yellobyte/ESP32-Webradio-PlusDLNA/Doc/ESP32-Radio Front.jpg

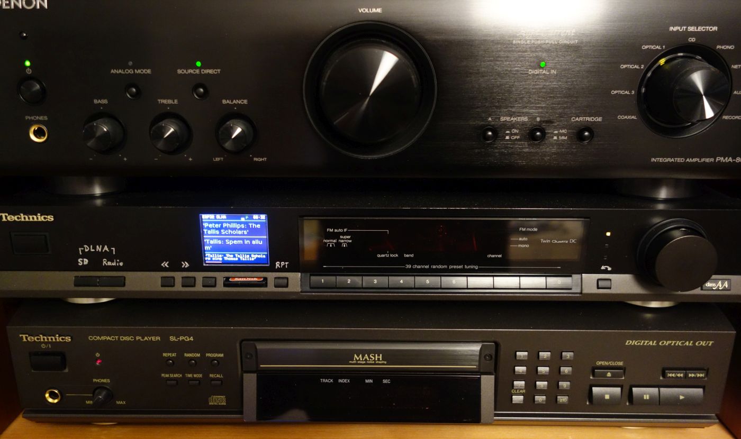
Doc/ESP32-Radio Front.jpg
