yellobyte/ESP32-Webradio-PlusDLNA/Doc/I2S to OPT Board Bottom.JPG

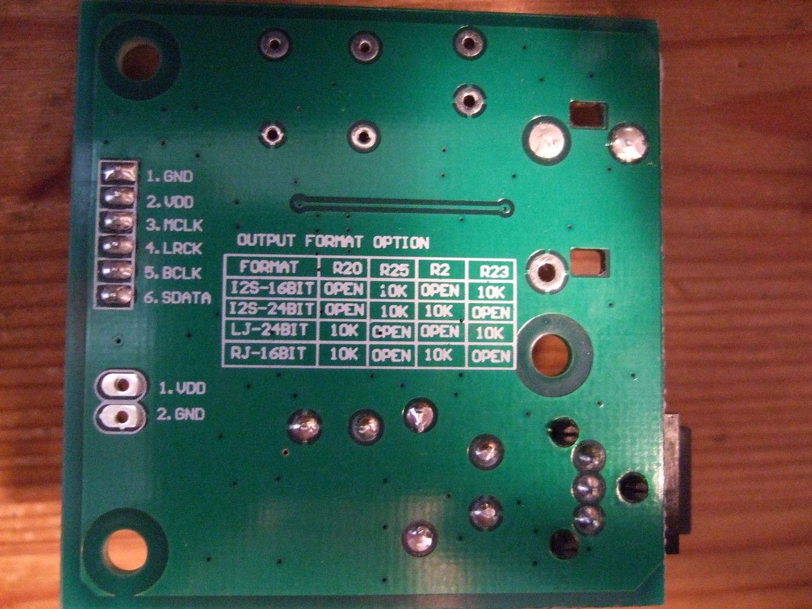
Doc/I2S to OPT Board Bottom.JPG
