yellobyte/ESP32-Webradio-PlusDLNA/Doc/I2S to OPT Board Top.JPG

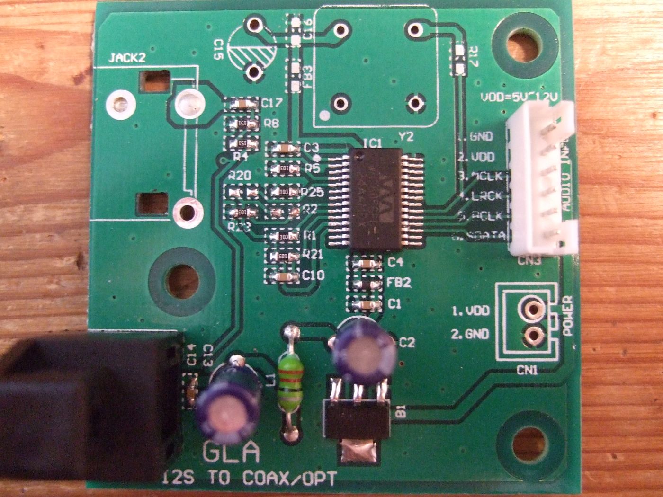
Doc/I2S to OPT Board Top.JPG
