yellobyte/ESP32-Webradio-PlusDLNA/Doc/Main Board.jpg

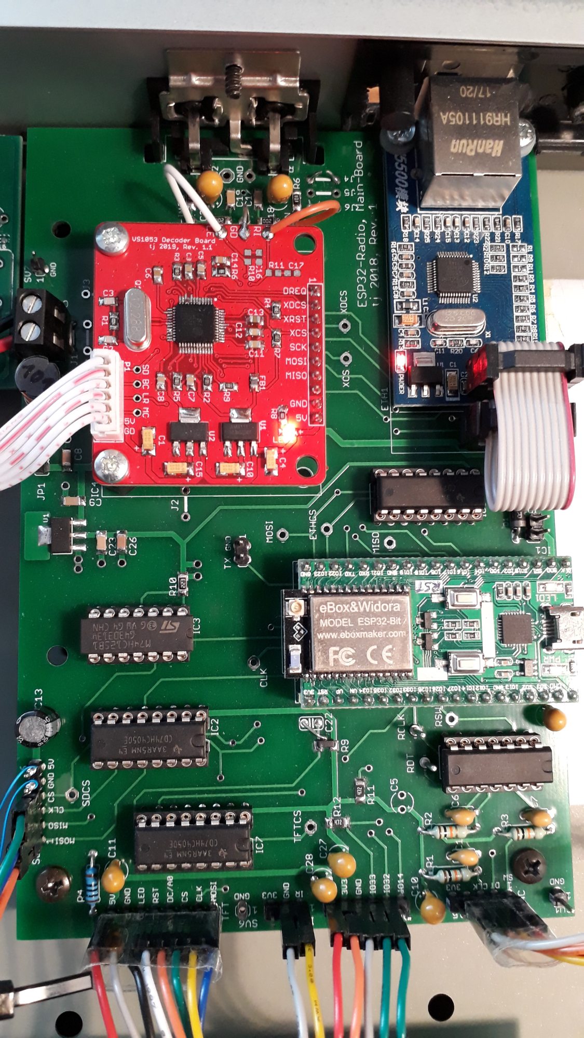
Doc/Main Board.jpg
