yellobyte/ESP32-Webradio-PlusDLNA/Doc/Open Case.jpg

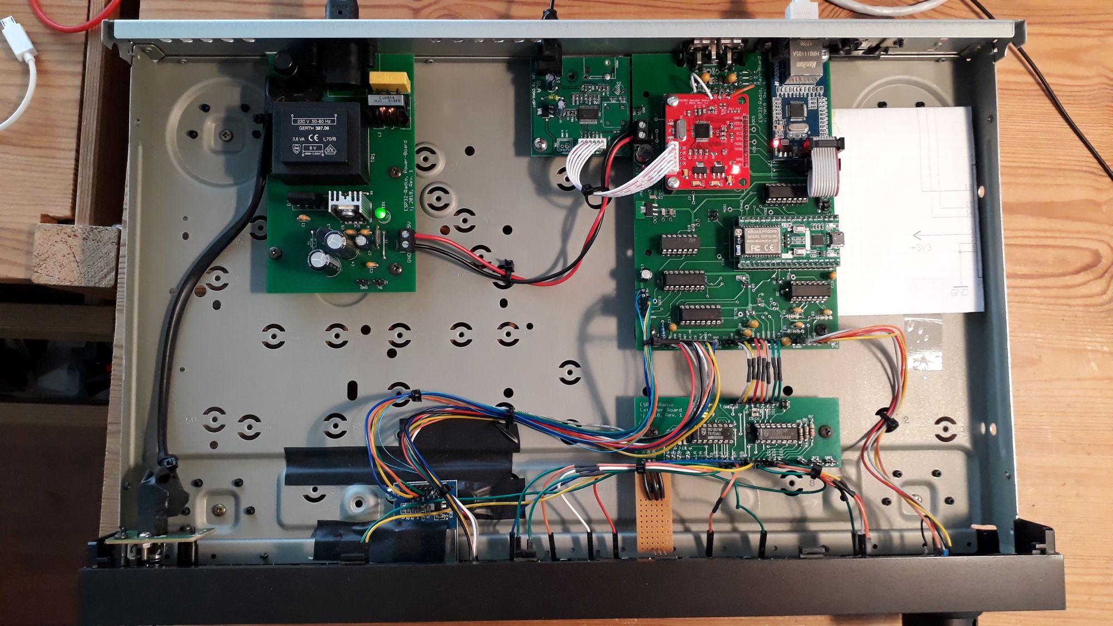
Doc/Open Case.jpg
