yellobyte/ESP32-Webradio-PlusDLNA/Doc/Power Board.jpg

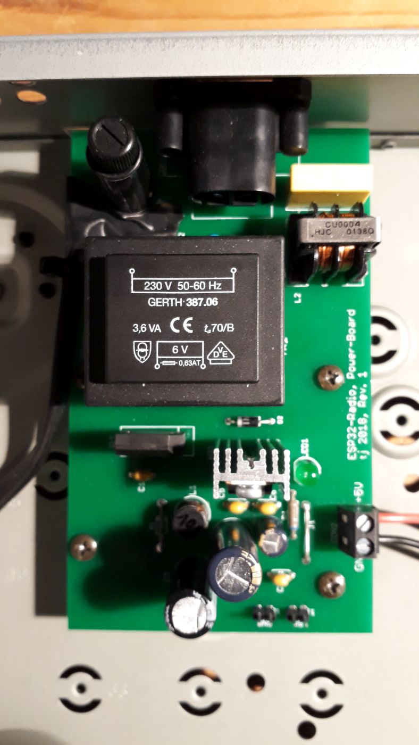
Doc/Power Board.jpg
