yellobyte/ESP32-Webradio-PlusDLNA/Doc/Rear view.jpg

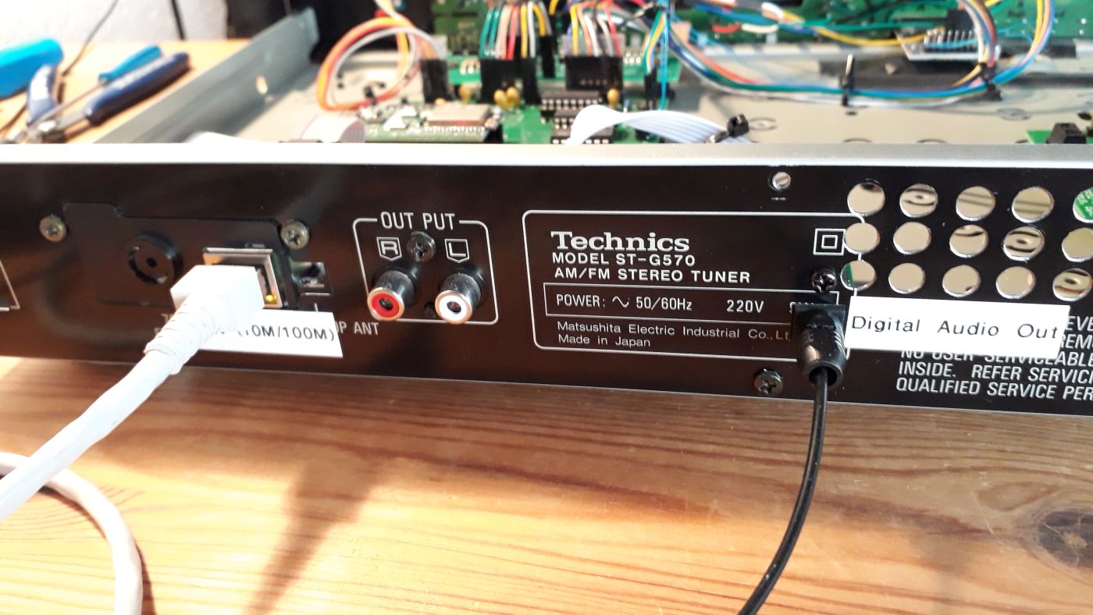
Doc/Rear view.jpg
