yellobyte/ESP32-Webradio-PlusDLNA/Doc/ST-G570 Original Case.jpg

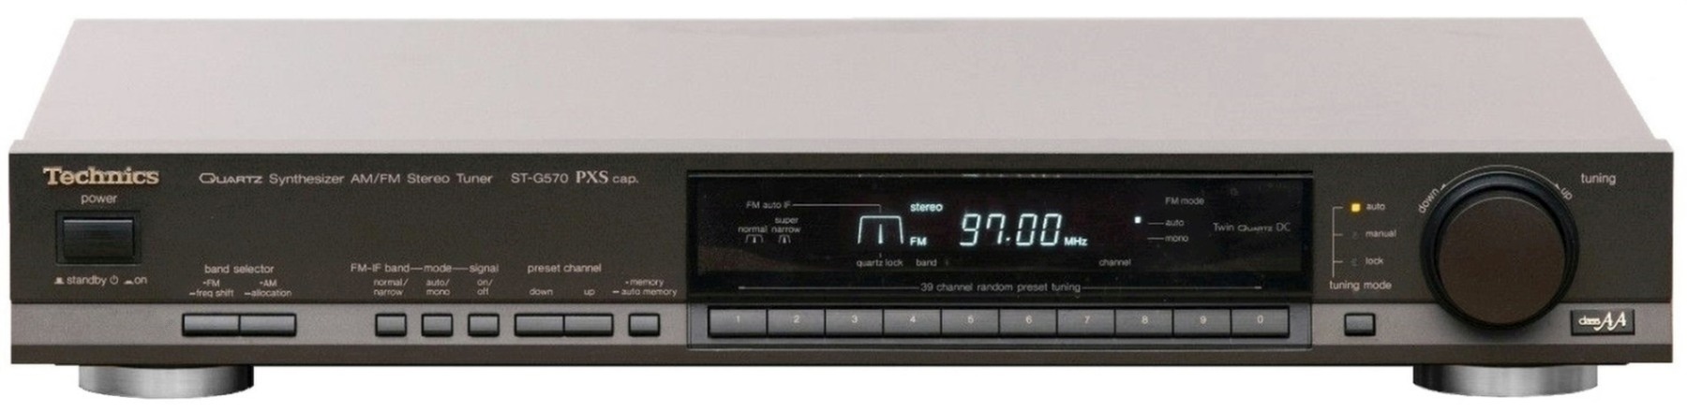
Doc/ST-G570 Original Case.jpg
