yellobyte/ESP32-Webradio-PlusDLNA/Doc/ST-G570 Original Inside.jpg

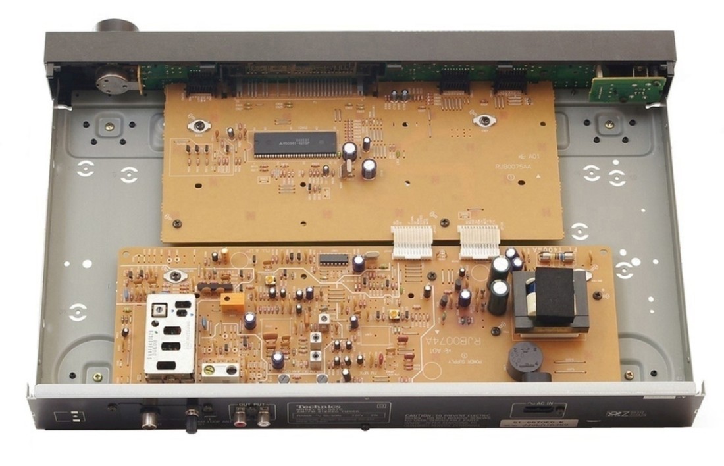
Doc/ST-G570 Original Inside.jpg
