yellobyte/ESP32-Webradio-PlusDLNA/EagleFiles/Extender-PCB/Board.JPG

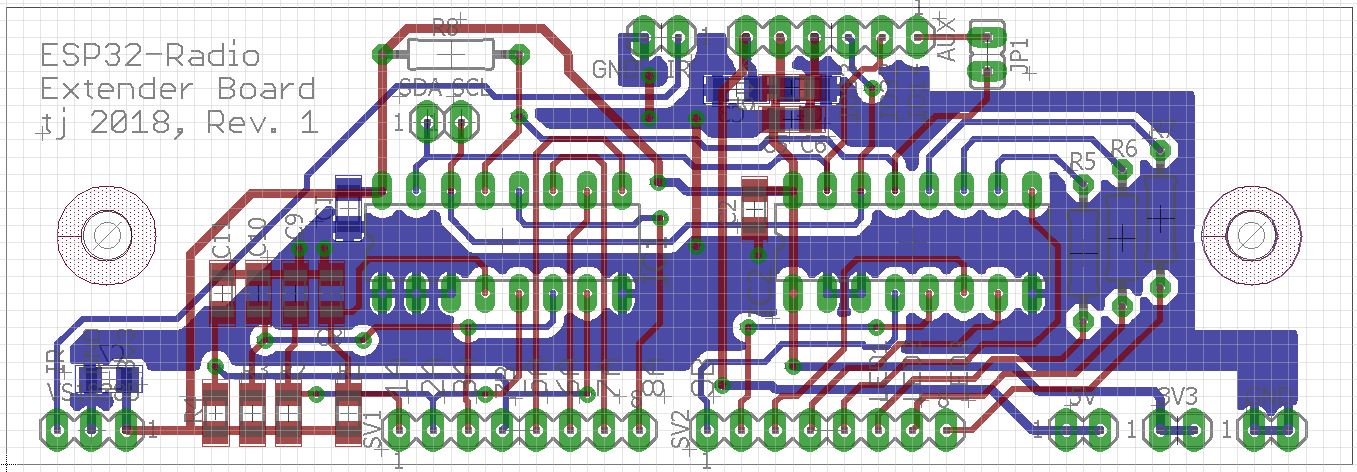
EagleFiles/Extender-PCB/Board.JPG
