yellobyte/ESP32-Webradio-PlusDLNA/EagleFiles/Extender-PCB/Distance.JPG

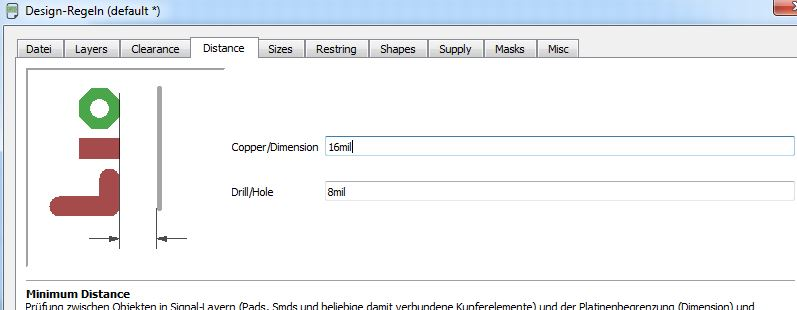
EagleFiles/Extender-PCB/Distance.JPG
