yellobyte/ESP32-Webradio-PlusDLNA/EagleFiles/Extender-PCB/Restring.JPG

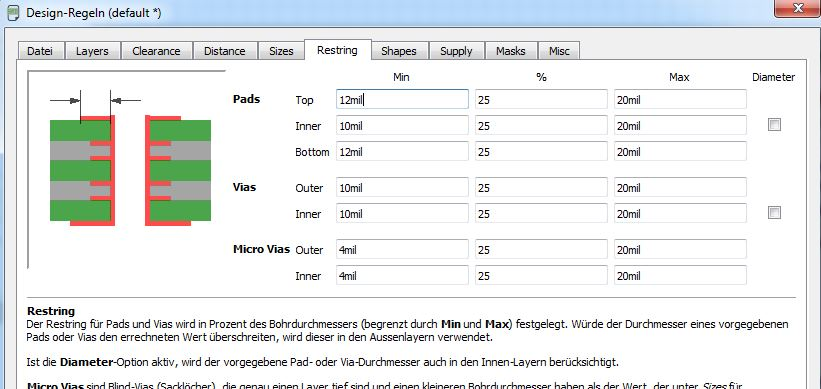
EagleFiles/Extender-PCB/Restring.JPG
