yellobyte/ESP32-Webradio-PlusDLNA/EagleFiles/Main-PCB/Board1.JPG

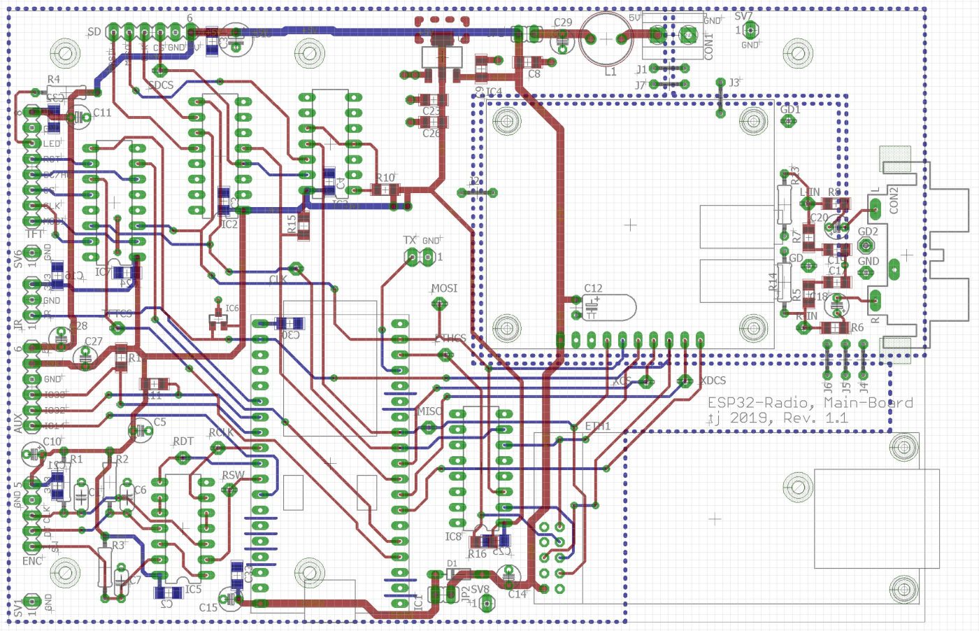
EagleFiles/Main-PCB/Board1.JPG
