yellobyte/ESP32-Webradio-PlusDLNA/EagleFiles/Main-PCB/Board2.JPG

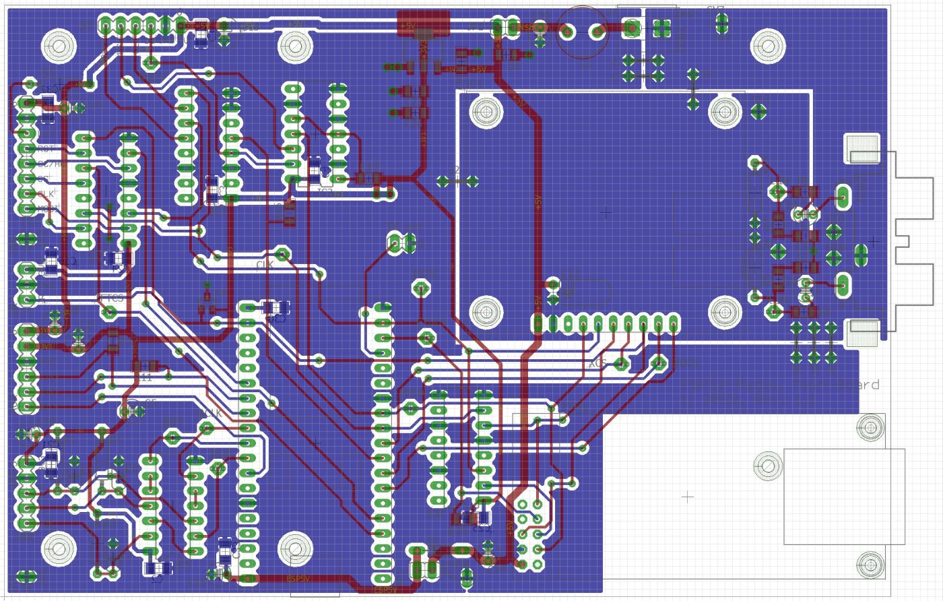
EagleFiles/Main-PCB/Board2.JPG
