yellobyte/ESP32-Webradio-PlusDLNA/EagleFiles/Main-PCB/Design-Clearance.JPG

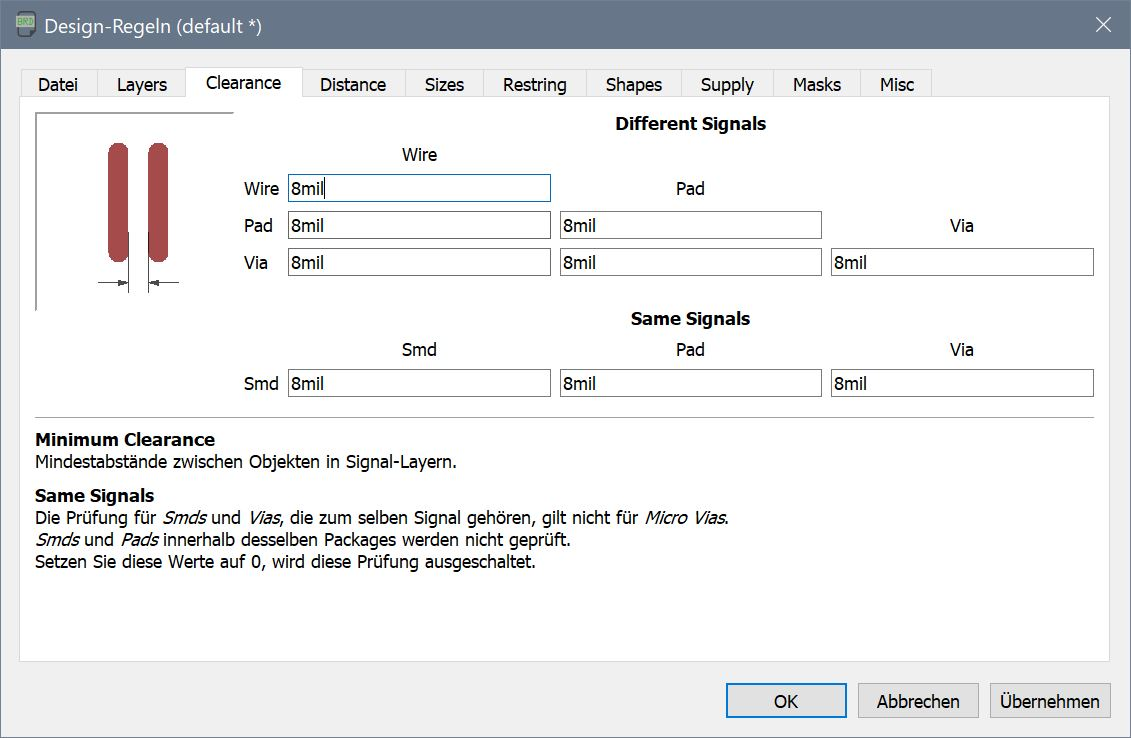
EagleFiles/Main-PCB/Design-Clearance.JPG
