yellobyte/ESP32-Webradio-PlusDLNA/EagleFiles/Main-PCB/Design-Masks.JPG

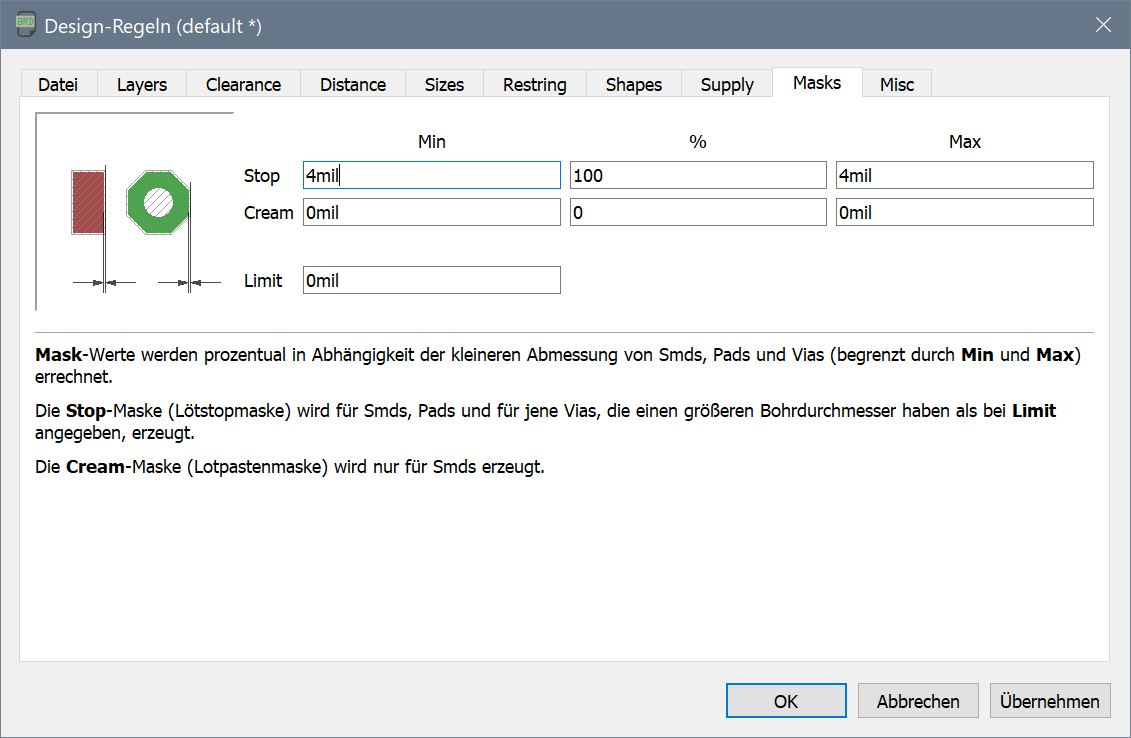
EagleFiles/Main-PCB/Design-Masks.JPG
