yellobyte/ESP32-Webradio-PlusDLNA/EagleFiles/Main-PCB/Design-Shapes.JPG

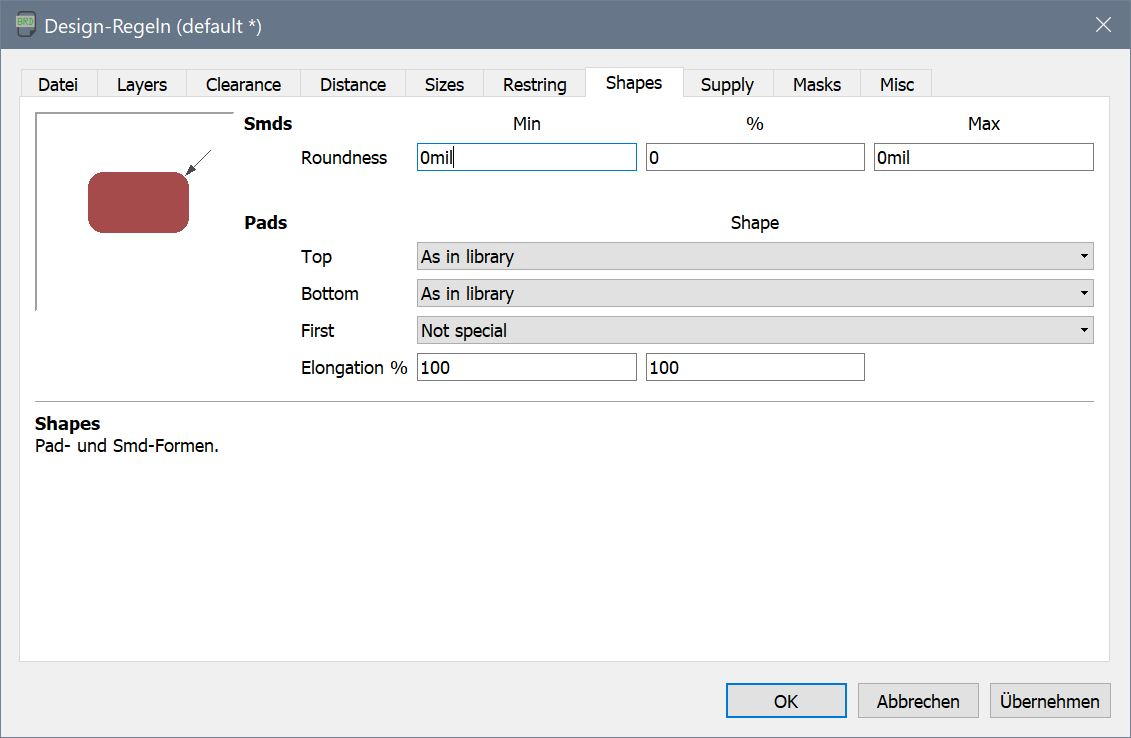
EagleFiles/Main-PCB/Design-Shapes.JPG
