yellobyte/ESP32-Webradio-PlusDLNA/EagleFiles/Main-PCB/Design-Sizes.JPG

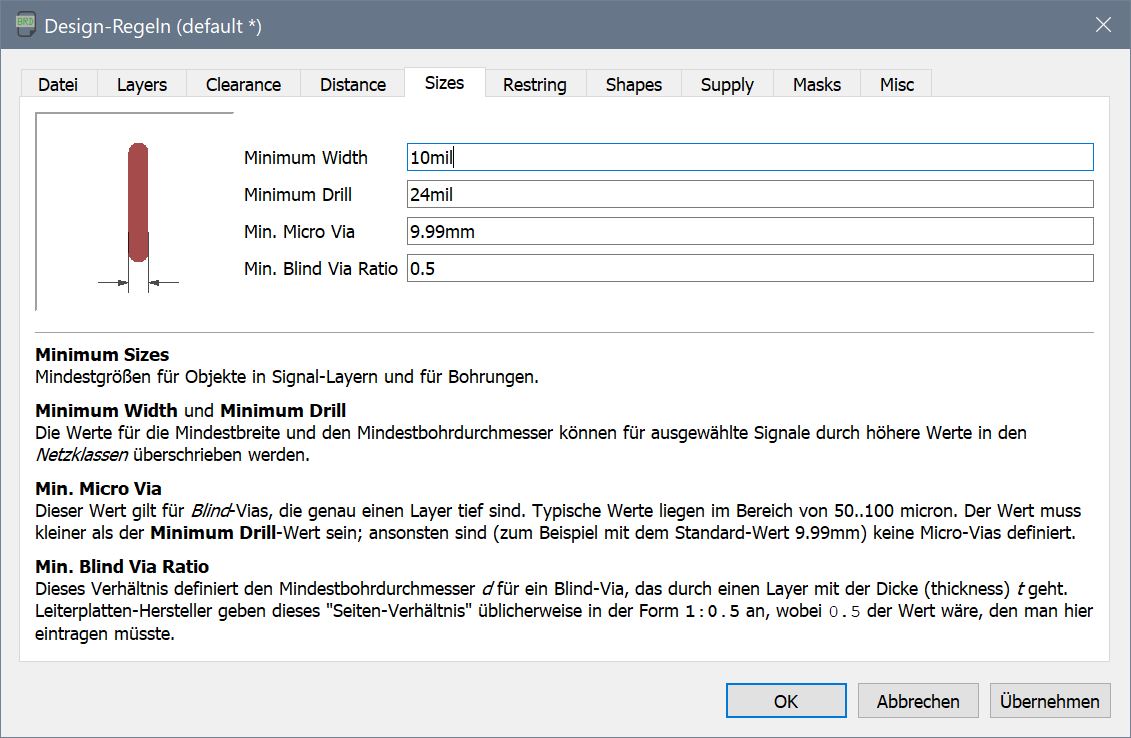
EagleFiles/Main-PCB/Design-Sizes.JPG
