yellobyte/ESP32-Webradio-PlusDLNA/EagleFiles/Main-PCB/Design-Supply.JPG

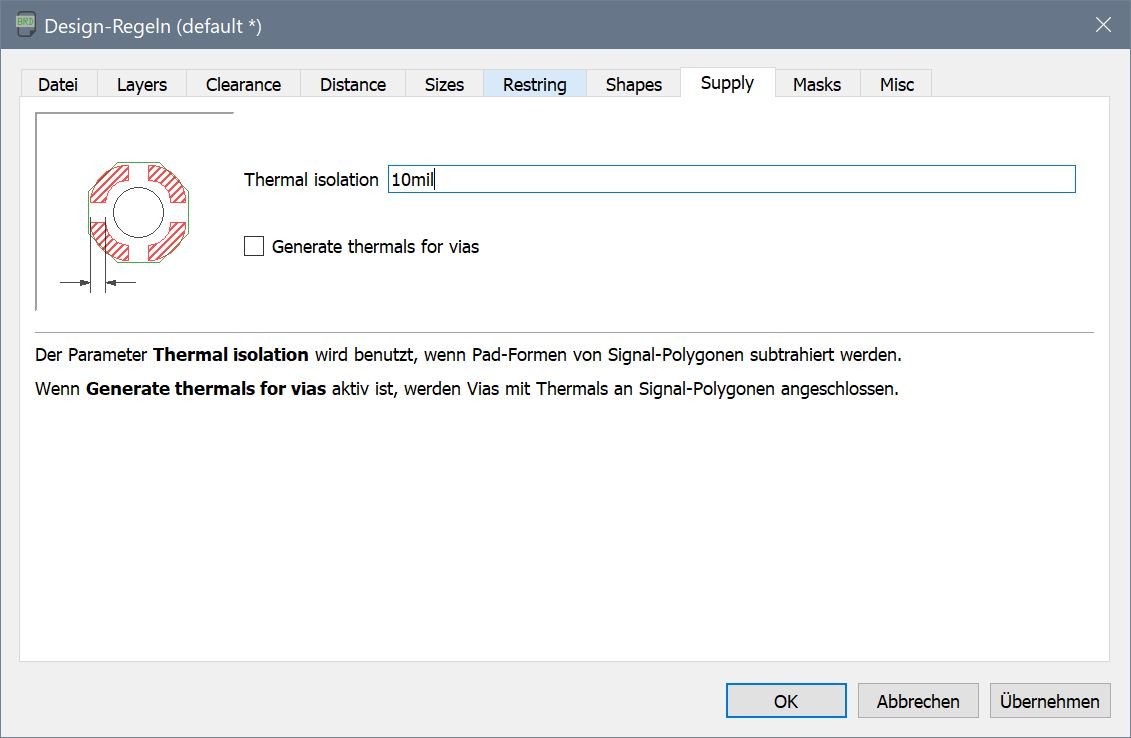
EagleFiles/Main-PCB/Design-Supply.JPG
