yellobyte/ESP32-Webradio-PlusDLNA/EagleFiles/Main-PCB/Net Classes.JPG

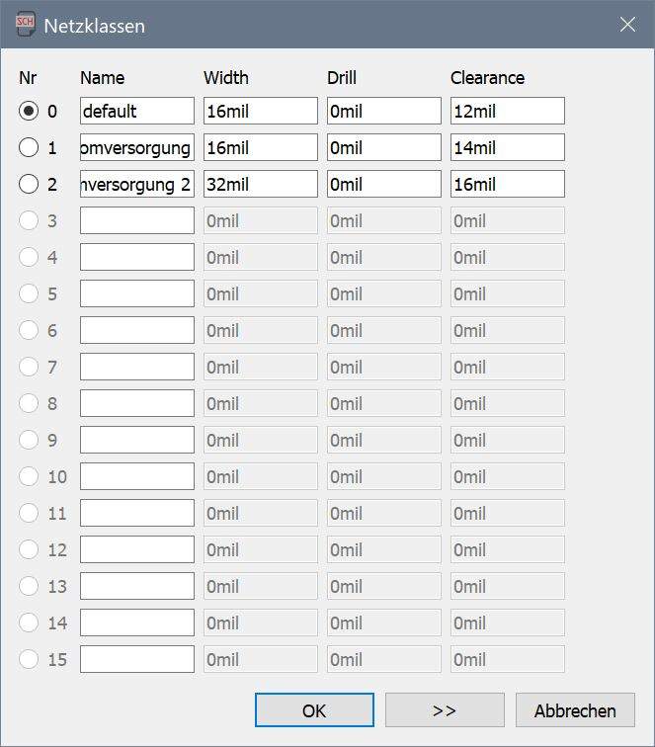
EagleFiles/Main-PCB/Net Classes.JPG
