yellobyte/ESP32-Webradio-PlusDLNA/EagleFiles/Power-PCB/Board.JPG

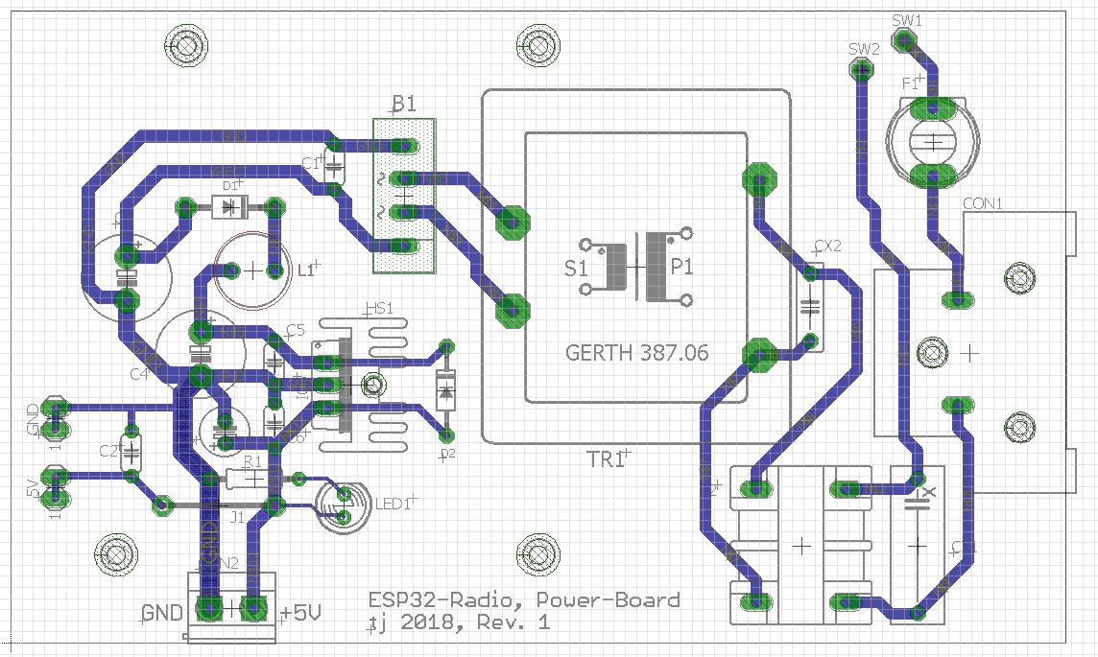
EagleFiles/Power-PCB/Board.JPG
