yellobyte/ESP32-Webradio-PlusDLNA/EagleFiles/Power-PCB/Schematic.JPG

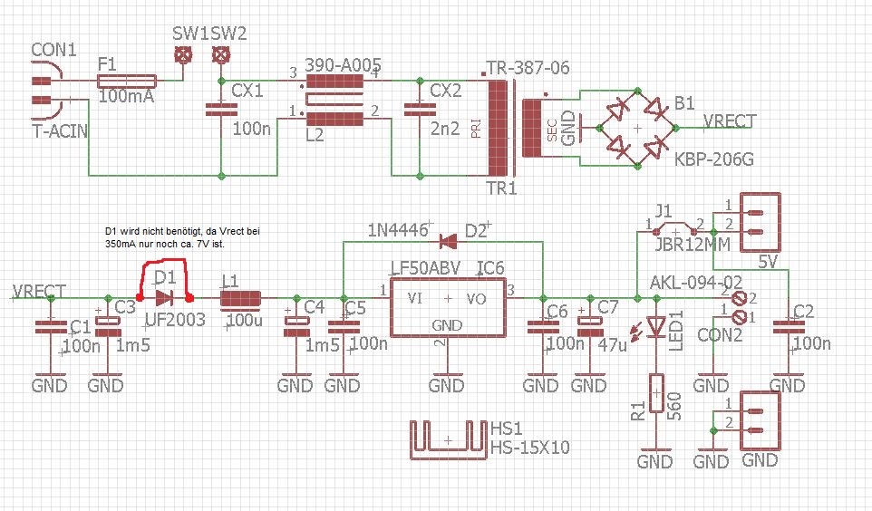
EagleFiles/Power-PCB/Schematic.JPG
