yellobyte/ESP32-Webradio-PlusDLNA/EagleFiles/VS1053-PCB/Board1.JPG

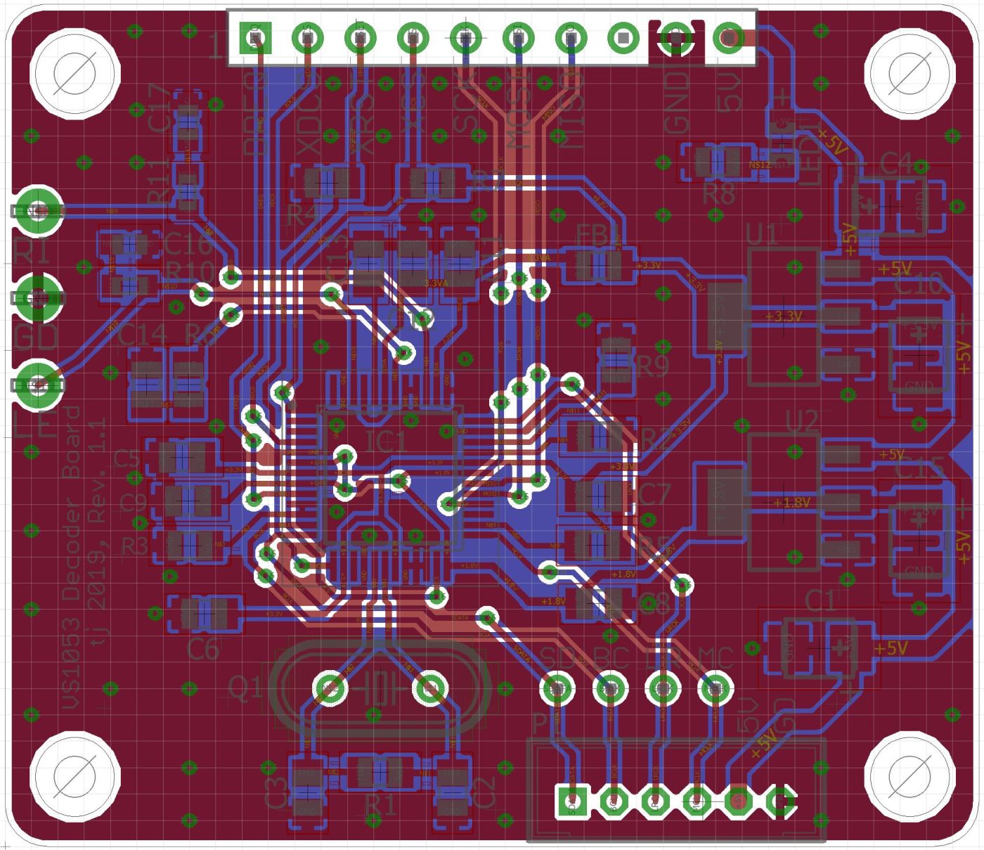
EagleFiles/VS1053-PCB/Board1.JPG
