yellobyte/ESP32-Webradio-PlusDLNA/EagleFiles/VS1053-PCB/Board2.JPG

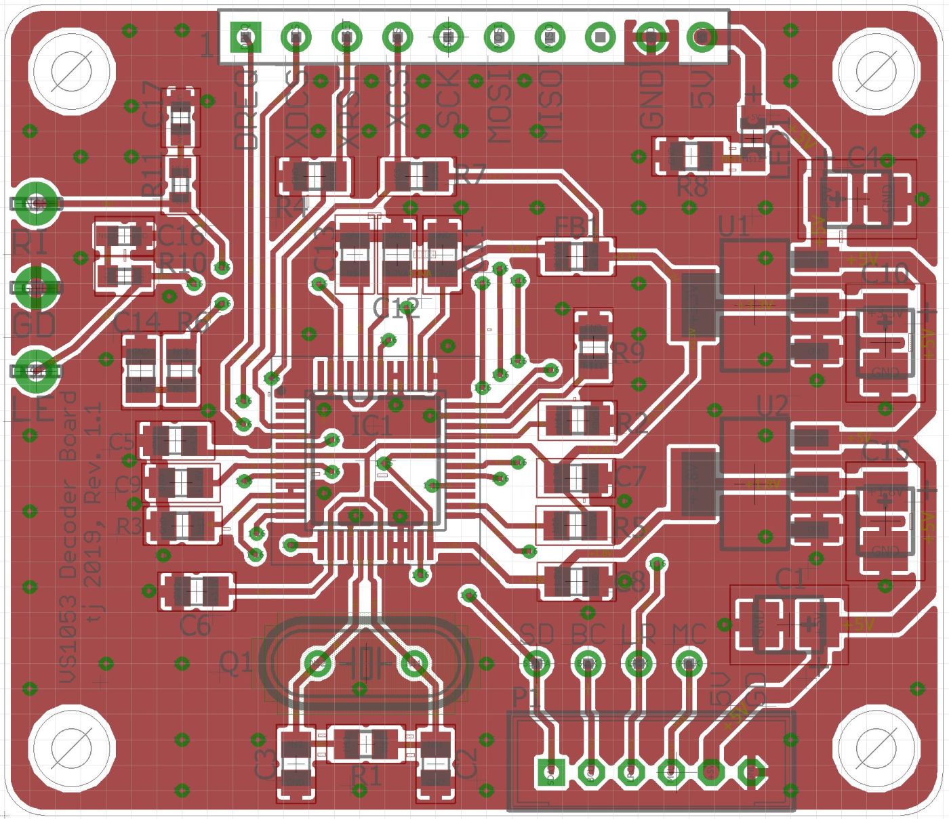
EagleFiles/VS1053-PCB/Board2.JPG
