yellobyte/ESP32-Webradio-PlusDLNA/Doc/First flying test set.JPG

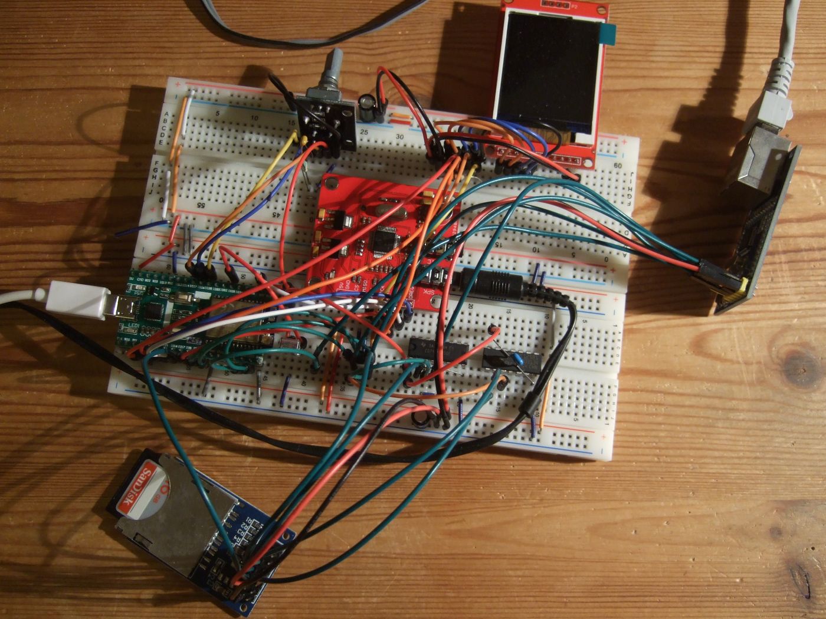
Doc/First flying test set.JPG
