yellobyte/ESP32-Webradio-PlusDLNA/Software/src/main.cpp

//*******************************************************************************************************
//*  ESP32 Webradio++                                                                                   *
//*                                                                                                     *
//*  For ESP32, 1.8 color display, VS1053 decoder module, Ethernet module and Optical digital audio     *
//*  output in an original Technics ST-G570 Radio Tuner case.                                           *
//*                                                                                                     *
//*  Based on Ed Smallenburgs (ed@smallenburg.nl) original ESP32 Radio project, version 10.06.2018.     * 
//*  His popular project is documented at https://github.com/Edzelf/ESP32-radio.                        *
//*                                                                                                     *
//*  Starting from Ed's code (Version 10.06.2018) this project has seen a lot of additions and          *
//*  modifications over time. Here a summary:                                                           *
//*   - DLNA/SOAP functionality added (utilizing SoapESP32 library)                                     *
//*   - Digital audio output added (TOSLINK optical) using a WM8805 module (China)                      *
//*   - Usage of own VS1053 decoder board (similar to China board but with I2S output and w/o sockets)  *
//*   - VS1053 gets patched with new firmware v2.7 at each reboot                                       *
//*   - VU meter added on TFT display (needs above mentioned firmware patch)                            *                           
//*   - Debug Server on port 23 for debug output (when compiled in than the cmd server is omitted)      *
//*   - Handling of original TECHNICS ST-G570 front panel buttons & LEDs via I2C and extender module    *
//*   - SD card indexing code rewritten in large parts                                                  *
//*   - Usage of W5500 Ethernet card instead of builtin WiFi                                            *
//*   - Ability to update ESP32 Radio code via SD card (using OTA functionality during reboot)          *
//*   - Encoder debouncing done completely in hardware (RC + Schmitt-Trigger IC), we use a Stec Rotary  *
//*     Encoder STEC11B03 with 1 impulse per 2 clicks                                                   *
//*   - MP3 progress bar while playing audio                                                            *
//*   - MQTT functionality & battery stuff removed completely                                           *
//*   - handling of more special chars in webradio streams (each channels seems to have a different     *
//*     utf8 conversion table or philosophy)                                                            *
//*   - countless minor changes & improvements, bugfixing                                               *
//*   - regular modifications for new espressif32 frameworks releases                                   *
//*  Have a look at "Revision history.txt" in the doc folder.                                           *
//*                                                                                                     *
//*  July 2022, TJ                                                                                      *
//*                                                                                                     *
//*******************************************************************************************************
//
// The standard Arduino Ethernet Library V2.0.x causes errors when compiled for an ESP32.
// File Ethernet.h needs to be modified. 
// Change line "class EthernetServer : public Server {"  to  "class EthernetServer : public Print {"
// and it will compile without problems.
//
// In Ethernet.h define MAX_SOCK_NUM 4  and  ETHERNET_LARGE_BUFFERS for better connection stability.
//
// SPI speed for the Ethernet Card is default 14MHz in W5100.h (Arduino Ethernet Library V2.0.0).
//
// Class 2 SD cards support at least 2MB/s (16Mbit/s) speed. Only 4MHz SPI clock speed is used here
// for stability reasons (long wires to SD-module).
//
// The VSPI interface is used for VS1053, TFT and SD. The I2C Arduino "Wire" Library was initially used for the
// extender card but proofed to be very unstable. Using low level I2C functions instead works a treat.
//
// Wiring. 
// Most pins (except 18,19,23 of the SPI interface) can be configured in the config page of the web interface.
// ESP32dev Signal  Wired to LCD    Wired to VS1053  SDCARD  Ethernet   Wired to the rest
// -------- ------  -------------   ---------------  ------  ---------  ------
// GPIO16           -               XDCS             -       -          -
// GPIO5            -               XCS              -       -          -
// GPIO4            -               DREQ             -       -          -
// GPIO2            D/C, RS or A0   -                -       -          -
// GPIO17           -               -                CS      -          -
// GPIO18   SCK     CLK or SCK      SCK              SCK     SCLK       -
// GPIO19   MISO    -               MISO             MISO    MISO       -
// GPIO23   MOSI    DIN or SDA      MOSI             MOSI    MOSI       -
// GPIO15   -       CS              -                -       -          -
// GPIO22   -       -               -                -       SCS        -
// GPI03    RXD0    -               -                -       -          Reserved
// GPIO1    TXD0    -               -                -       -          Reserved
// GPIO34   -       -               -                -       -          Reserved
// GPIO35   -       -               -                -       -          Infrared receiver VS1838B
// GPIO25   -       -               -                -       -          Rotary encoder CLK
// GPIO26   -       -               -                -       -          Rotary encoder DT
// GPIO27   -       -               -                -       -          Rotary encoder SW
// GPIO32   SDA     -               -                -       -          I2C-SDA Extenderboard
// GPIO33   SCL     -               -                -       -          I2C-SCL Extenderboard
// -------  ------  -------------   ---------------  ------  ---------  ----------------
// GND      -       GND             GND              GND     GND        Power supply GND
// VCC 5 V  -       BL              -                +5      5V         Power supply
// VCC 5 V  -       VCC             5V               -       -          Power supply
// EN       -       RST             XRST             -       RST        -
// 3.3 V    -       -               -                -       -          Rotary Encoder, 74HC4050, 74HC125
//
//

// Define the version number, also used for webserver as Last-Modified header:
#define VERSION "11 Jan 2024 09:15"
//
// Defined in platform.ini as it affects soapESP32 too !
//#define USE_ETHERNET                   // Use Ethernet/LAN instead of WiFi builtin
// 

#define ENABLE_CMDSERVER               // Enable port 80 web server (Control Website)
#define ENABLE_SOAP                    // Enable SOAP/DLNA access to media server
//#define ENABLE_INFRARED                // Enable remote control functionality per IR
//#define ENABLE_DIGITAL_INPUTS          // If we want to use digital inputs to start actions/commands
//#define PORT23_ACTIVE                  // Configure Server on port 23 for sending debug messages
//#define CHECK_LOOP_TIME                // Checking loop round time for debugging purposes
#define ENABLE_I2S                     // Activates I2S on VS1053B for communication with WM8805 module (I2S/OPT)
#define LOAD_VS1053_PATCH              // Loads a patch into the VS1053 which fixes the SS_REFERENCE_SEL bug
#define VU_METER                       // Displays VU-Meter levels provided by VS1053B
#define SD_UPDATES                     // SW-Updates via SD-Card during power-up
#define ENABLE_ESP32_HW_WDT            // Enable ESP32 Hardware Watchdog
#define FRONT_PANEL_BUTTONS            // Use front panel buttons

#include <Arduino.h>
//#include <FS.h>
//#include <SPI.h>
#include <SD.h>
#include <nvs.h>
#include <stdio.h>
#include <string.h>
#ifdef SD_UPDATES
#include <Update.h>
#define UPDATE_FILE_NAME "/firmware.bin"
#define TEST_FILE_NAME "/testfile.txt"
#endif
#ifndef USE_ETHERNET
#include <WiFiMulti.h>
#include <ESPmDNS.h>
#include <ArduinoOTA.h>
#else
#include <WiFi.h>
#include <vector>
#endif
#include <time.h>
#include <freertos/queue.h>
#include <freertos/task.h>
#ifdef ENABLE_ESP32_HW_WDT
#include <esp_task_wdt.h>
#endif
#include <esp_partition.h>
#include "driver/i2c.h"

#ifdef USE_ETHERNET
#include <Ethernet.h>
#include <EthernetUdp.h>
byte mac[] = {0xDE, 0xAD, 0xBE, 0xEF, 0xFE, 0xED};
#define _claimSPI(p)  claimSPI(p)    // mp3client.read() sometimes returns garbage without it
#define _releaseSPI() releaseSPI()
#else
#define _claimSPI(p)
#define _releaseSPI()
#endif
#ifdef ENABLE_SOAP
#include "SoapESP32.h"
#endif

// comment out if ESP_EARLY_LOGx not needed
//#define LOG_LOCAL_LEVEL ESP_LOG_DEBUG
//#include "esp_log.h"
//DRAM_ATTR static const char* TAG = "ESP32Radio";

// ESP32 hardware watchdog timeout
#define WDT_TIMEOUT 60
// Number of entries in the queue
#define QSIZ 1000
// Debug buffer size
#define DEBUG_BUFFER_SIZE 250
// Access point name if connection to WiFi network fails.  Also the hostname for WiFi and OTA.
// Not that the password of an AP must be at least as long as 8 characters.
// Also used for other naming.
#define NAME "ESP32Radio"
// Adjust size of buffer to the longest expected string for nvsgetstr
#define NVSBUFSIZE 150
// Position (column) of time in topline relative to end
#define TIMEPOS -30
// SPI speed for SD card, (8 MHz still working fine on breadboard)
#define SDSPEED 4000000
// Size of metaline buffer
#define METASIZ 1024
// Max. number of NVS keys in table
#define MAXKEYS 200
// Max. node depth on SD card we will recognize
#define SD_MAXDEPTH 4
// Max mp3-files to recognize on SD card (we skip all the others)
#define SD_MAXFILES 500
//length of longest debug command string plus two spaces for CR + LF (from client on port 23)
#define MAXSIZE_TELNET_CMD 10 
// defaults, can be overridden by preferences
IPAddress local_IP(192, 168, 1, 99);
IPAddress gateway(192, 168, 1, 1);
IPAddress subnet(255, 255, 255, 0);
IPAddress primaryDNS(192, 168, 1, 1);
IPAddress secondaryDNS(195, 186, 4, 162);     //optional
#define NTP_SERVER_DEFAULT "ptbtime1.ptb.de"  // time-a.timefreq.bldrdoc.gov, pool.ntp.org, etc.....
#ifdef USE_ETHERNET
#define NTP_TZ_STRING_DEFAULT "CET-1CEST-2,M3.5.0/02:00:00,M10.5.0/03:00:00"
#endif
// Position (column) in topline relative to end
#define MUTEPOS     -42
#define SDSTATUSPOS -49
#if defined VU_METER && defined LOAD_VS1053_PATCH
#define VUMETERPOS  -61
#endif
// I2C stuff: PCF8574 Addresses & assigned Pins
#define PCF8574_1_ADDR (0x20)
#define PCF8574_2_ADDR (0x21)
#define I2C_SDA_PIN  32
#define I2C_SCL_PIN  33
#ifdef ENABLE_SOAP
// Default SOAP/DLNA media server settings
// parameters for Twonky media server on QNAP TS-253D
#define MEDIASERVER_DEFAULT_MAC "24:5E:BE:5D:2F:66"
#define MEDIASERVER_DEFAULT_IP 192,168,1,11
#define MEDIASERVER_DEFAULT_PORT 9000
#define MEDIASERVER_DEFAULT_CONTROL_URL "dev0/srv1/control"
#endif
//
//
//**************************************************************************************************
// Forward declaration and prototypes of various functions.                                        *
//**************************************************************************************************
void        displayTime(const char* str, uint16_t color = 0xFFFF);
void        showStreamTitle(const char* ml, bool full = false);
void        handlebyte_ch(uint8_t b);
void        handleFSf(const String& pagename);
void        handleCmd();
char*       dbgprint(const char* format, ...);
const char* analyzeCmd(const char* str);
const char* analyzeCmd(const char* par, const char* val);
void        chomp(String &str);
String      limitString(String& strg, int maxPixel);
String      httpHeader(String contentstype);
bool        nvsSearch(const char* key);
void        mp3loop();
//void        tftlog(const char *str, uint16_t textColor = (WHITE));
void        playTask(void * parameter);       // Task to play the stream
void        spfTask(void * parameter);        // Task for special functions
void        getTime();
#ifdef FRONT_PANEL_BUTTONS			
void        extenderTask(void * parameter);   // Task for communication with PCF8574 ICs
#endif			
void        vumeterTask(void * parameter);    // Task for showing vu meter readings
bool        handlePCF8574();
#ifdef USE_ETHERNET
void        tzset(void);
int         setenv(const char *name, const char *value, int overwrite);
#endif

//**************************************************************************************************
// Several structs.                                                                                *
//**************************************************************************************************
//

struct scrseg_struct                                 // For screen segments
{
  bool     update_req;                               // Request update of screen
  uint16_t color;                                    // Textcolor
  uint16_t y;                                        // Begin of segment row
  uint16_t height;                                   // Height of segment
  String   str;                                      // String to be displayed (Name)
};

enum qdata_type { QDATA, QSTARTSONG, QSTOPSONG };    // datatyp in qdata_struct
struct qdata_struct
{
  int datatyp;                                       // Identifier
  __attribute__((aligned(4))) uint8_t buf[32];       // Buffer for chunk
};

struct ini_struct
{
  uint8_t        reqvol;                             // Requested volume
  uint8_t        rtone[4];                           // Requested bass/treble settings
  int8_t         newpreset;                          // Requested preset
#ifdef USE_ETHERNET
  String         clk_tzstring;                       // Posix timezone string
#else
  int8_t         clk_offset;                         // Offset in hours with respect to UTC
  int8_t         clk_dst;                            // Number of hours shift during DST
#endif
  String         clk_server;                         // Server to be used for time of day clock
#ifdef ENABLE_SOAP
  IPAddress      srv_ip;                             // media server ip
  uint16_t       srv_port;                           // media server port
  String         srv_controlUrl;                     // media server control URL
  String         srv_macWOL;                         // mac needed to send WOL packets to media server
#endif
#ifdef ENABLE_INFRARED
  int8_t         ir_pin;                             // GPIO connected to output of IR decoder
#endif  
  int8_t         enc_clk_pin;                        // GPIO connected to CLK of rotary encoder
  int8_t         enc_dt_pin;                         // GPIO connected to DT of rotary encoder
  int8_t         enc_sw_pin;                         // GPIO connected to SW of rotary encoder
  int8_t         tft_cs_pin;                         // GPIO connected to CS of TFT screen
  int8_t         tft_dc_pin;                         // GPIO connected to D/C or A0 of TFT screen
  int8_t         sd_cs_pin;                          // GPIO connected to CS of SD card
  int8_t         vs_cs_pin;                          // GPIO connected to CS of VS1053
  int8_t         vs_dcs_pin;                         // GPIO connected to DCS of VS1053
  int8_t         vs_dreq_pin;                        // GPIO connected to DREQ of VS1053
  int8_t         vs_shutdown_pin;                    // GPIO to shut down the amplifier
  int8_t         spi_sck_pin;                        // GPIO connected to SPI SCK pin
  int8_t         spi_miso_pin;                       // GPIO connected to SPI MISO pin
  int8_t         spi_mosi_pin;                       // GPIO connected to SPI MOSI pin
};

#ifndef USE_ETHERNET
struct WifiInfo_t                                     // For list with WiFi info
{
  uint8_t inx;                                       // Index as in "wifi_00"
  char * ssid;                                       // SSID for an entry
  char * passphrase;                                 // Passphrase for an entry
};
#endif

struct nvs_entry
{
  uint8_t  Ns;                                       // Namespace ID
  uint8_t  Type;                                     // Type of value
  uint8_t  Span;                                     // Number of entries used for this item
  uint8_t  Rvs;                                      // Reserved, should be 0xFF
  uint32_t CRC;                                      // CRC
  char     Key[16];                                  // Key in Ascii
  uint64_t Data;                                     // Data in entry
};

struct nvs_page                                       // For nvs entries
{ // 1 page is 4096 bytes
  uint32_t  State;
  uint32_t  Seqnr;
  uint32_t  Unused[5];
  uint32_t  CRC;
  uint8_t   Bitmap[32];
  nvs_entry Entry[126];
};

struct keyname_t                                      // For keys in NVS
{
  char Key[16];                                       // Mac length is 15 plus delimeter
};

struct mp3node_t                                      // for directories/files on SD card
{
  bool    isDirectory;                                // node is file or directory
  int16_t parentDir;                                  // which directory is it in
  String  name;                                       // file/directory name
};

#ifdef ENABLE_SOAP
struct soapChain_t
{
  String id;
  String name;
  size_t size;
  size_t startingIndex;
};
#endif

//**************************************************************************************************
// Global data section.                                                                            *
//**************************************************************************************************
// There is a block ini-data that contains some configuration.  Configuration data is              *
// saved in the preferences by the webinterface.  On restart the new data will                     *
// de read from these preferences.                                                                 *
// Items in ini_block can be changed by commands from webserver or Serial.                         *
//**************************************************************************************************

enum enum_datamode { INIT = 1, HEADER = 2, DATA = 4,     // State for datastream
                     METADATA = 8, PLAYLISTINIT = 16,
                     PLAYLISTHEADER = 32, PLAYLISTDATA = 64,
                     STOPREQD = 128, STOPPED = 256, CONNECTERROR = 512 };
enum enum_enc_menu { IDLING, SELECT };                   // State for rotary encoder menu
enum enum_selection { NONE, STATION, SDCARD, MEDIASERVER }; // play mode or selected source
enum enum_repeat_mode { NOREPEAT, SONG, DIRECTORY, RANDOM }; // repeat mode

// Global variables
int               DEBUG = 1;                             // Debug on/off
int               numSsid;                               // Number of available WiFi networks
ini_struct        ini_block;                             // Holds configurable data
#ifndef USE_ETHERNET
WiFiMulti         wifiMulti;                             // Possible WiFi networks
#if defined(ENABLE_CMDSERVER) && !defined(PORT23_ACTIVE)
WiFiServer        cmdserver(80);                         // Instance of embedded webserver, port 80
WiFiClient        cmdclient;                             // An instance of the client for commands
#endif
#ifdef PORT23_ACTIVE
WiFiServer        dbgserver(23);                         // Instance of server, telnet port 23
WiFiClient        dbgclient;                             // An instance of the debug/telnet client
bool              dbgConnectFlag = false;                // true if client connected on port 23
#endif
WiFiClient        mp3client;                             // An instance of the mp3 client
#else 
// we use Ethernet/LAN
#if defined(ENABLE_CMDSERVER) && !defined(PORT23_ACTIVE)
EthernetServer    cmdserver(80);                         // Instance of embedded webserver, port 80
EthernetClient    cmdclient;                             // An instance of the client for commands
#endif
#ifdef PORT23_ACTIVE
EthernetServer    dbgserver(23);                         // Instance of server, telnet port 23
EthernetClient    dbgclient;                             // An instance of the debug/telnet client
bool              dbgConnectFlag = false;                // true if client connected on port 23
#endif
EthernetClient    mp3client;                             // An instance of the mp3 client
EthernetUDP       udpclient;                             // A UDP instance used for ntp time retrieval
EthernetLinkStatus lstat;                                // Ethernet link status
bool              reInitEthernet = false;                // W5500 board re-initialization needed
#endif
TaskHandle_t      mainTask;                              // Taskhandle for main task
TaskHandle_t      xplayTask;                             // Task handle for play task
TaskHandle_t      xspfTask;                              // Task handle for special functions
#ifdef FRONT_PANEL_BUTTONS													
TaskHandle_t      xextenderTask;                         // Task handle for communication with PCF8574 ICs
#endif			
#if defined VU_METER && defined LOAD_VS1053_PATCH
TaskHandle_t      xvumeterTask;                          // Task handle for displaying vu-meter value
#endif
SemaphoreHandle_t SPIsem = NULL;                         // For exclusive SPI usage
hw_timer_t*       timer = NULL;                          // For timer
char              timetxt[6];                            // Converted timeinfo
QueueHandle_t     dataQueue;                             // Queue for mp3 datastream
qdata_struct      outchunk;                              // Data to queue
qdata_struct      inchunk;                               // Data from queue
uint8_t*          outqp = outchunk.buf;                  // Pointer to buffer in outchunk
uint32_t          totalCount = 0;                        // Counter mp3 data
enum_datamode     dataMode = STOPPED;                    // State of datastream
int               metacount;                             // Number of bytes in metadata
int               datacount;                             // Counter databytes before metadata
char              metalinebf[METASIZ + 1];               // Buffer for metaline/ID3 tags
int16_t           metalinebfx;                           // Index for metalinebf
String            icystreamtitle;                        // Streamtitle from metadata
String            icyname;                               // Icecast station name
String            ipaddress;                             // Own IP-address
int               bitrate;                               // Bitrate in kb/sec
int               mbitrate;                              // Measured bitrate
int               metaint = 0;                           // Number of databytes between metadata
int8_t            currentPreset = -1;                    // Preset station playing
int8_t            highestPreset = 0;                     // highest preset
String            host;                                  // The URL to connect to or file to play
String            playlist;                              // The URL of the specified playlist
bool              hostreq = false;                       // Request for new host
bool              reqtone = false;                       // New tone setting requested
int8_t            muteFlag = 0;                          // Mute output (0=unmuted, -1=permanently, >0 temp. in 1/10 sec)
bool              resetreq = false;                      // Request to reset the ESP32
bool              NetworkFound = false;                  // True if WiFi network connected
String            networks;                              // Found networks in the surrounding
int8_t            playlist_num = 0;                      // Nonzero for selection from playlist
File              mp3file;                               // File containing mp3 on SD card
size_t            mp3fileLength;                         // File length
size_t            mp3fileBytesLeft;                      // Still to read
enum_selection    currentSource = NONE;                  // momentary source we play from at this moment
bool              chunked = false;                       // Station provides chunked transfer
int               chunkcount = 0;                        // Counter for chunked transfer
String            http_getcmd;                           // Contents of last GET command
String            http_rqfile;                           // Requested file
bool              http_reponse_flag = false;             // Response required
#ifdef ENABLE_INFRARED
uint16_t          ir_value = 0;                          // IR code
uint32_t          ir_0 = 550;                            // Average duration of an IR short pulse
uint32_t          ir_1 = 1650;                           // Average duration of an IR long pulse
#endif
struct tm         timeinfo;                              // Will be filled by NTP server
bool              time_req = false;                      // Set time requested
bool              SD_okay = false;                       // True if SD card in place and readable
int16_t           SD_mp3fileCount = 0;                   // Number of mp3 files found
int16_t           currentIndex = -1;                     // current index in mp3List when SD (0 means random) and in soapList when Mediaserver
uint16_t          clength;                               // Content length found in http header
enum_repeat_mode  mp3fileRepeatFlag = NOREPEAT;
bool              mp3fileJumpForward = false;            // jump forward in mp3 file
bool              mp3fileJumpBack = false;               // jump backwards in mp3 file
bool              mp3filePause = false;                  // pause playing mp3 file
bool              staticIPs = false;
bool              dhcpRequested = false;
String            sdOutbuf;                              // Output buffer for cmdclient
String            lastArtistSong;                        // for restoring text after timeout
String            lastAlbumStation;                      // for restoring text after timeout
bool              tryToMountSD = false;                  // request to mount SD when system is already up and running
bool              forceProgressBar = false;              // request progress bar to be painted
std::vector<mp3node_t> mp3nodeList;
#ifndef USE_ETHERNET
std::vector<WifiInfo_t> wifilist;                        // List with wifi_xx info
#else
unsigned int      localPortNtp = 8888;                   // local port to listen for UDP packets
const int         NTP_PACKET_SIZE = 48;                  // NTP time stamp is in the first 48 bytes of the message
#endif
// nvs stuff
nvs_page               nvsbuf;                           // Space for 1 page of NVS info
const esp_partition_t* nvs;                              // Pointer to partition struct
esp_err_t              nvserr;                           // Error code from nvs functions
uint32_t               nvshandle = 0;                    // Handle for nvs access
uint8_t                namespaceID;                      // Namespace ID found
char                   nvskeys[MAXKEYS][16];             // Space for NVS keys
std::vector<keyname_t> keynames;                         // Keynames in NVS
// Rotary encoder & front panel stuff
#define sv DRAM_ATTR static volatile
sv uint16_t       clickcount = 0;                        // Incremented per encoder click
sv int16_t        rotationcount = 0;                     // Current position of rotary switch
sv uint16_t       enc_inactivity = 0;                    // Time inactive
sv bool           singleClick = false;                   // True if single click detected
//sv bool           tripleclick = false;                  // True if triple click detected
sv bool           doubleClick = false;                   // True if double click detected
sv bool           longClick = false;                     // True if longClick detected
bool              buttonReturn = false;                  // True if return button pressed
bool              buttonRepeatMode = false;              // True if repeat button pressed
int8_t            buttonPreset = -1;                     // 0...9 if station button pressed
bool              buttonSD = false;                      // True if "SD" button presed
bool              buttonStation = false;                 // True if "Station" button pressed
//
#ifdef ENABLE_SOAP
#ifdef USE_ETHERNET
SoapESP32         soap(&mp3client, &udpclient, &SPIsem); // UDP/SSDP used only for WOL, global SPI lock 
#else
SoapESP32         soap(&mp3client, NULL);                // UDP/SSDP not used, no global SPI lock 
#endif
bool              buttonMediaserver = false;             // True if "SD" & "Station" buttons were pressed at once
std::vector<soapChain_t> soapChain;                      // For finding our way back up to root ("0")
soapObjectVect_t  soapList;                              // SOAP browse results for a given object (container/directory)
soapObject_t      hostObject;                            // more needed than just a string as for radio or SD card
#endif
bool              buttonSkipBack = false;                // True if "Skip Back" button is pressed
bool              buttonSkipForward = false;             // True if "Skip Forward" button is pressed
bool              skipStationAllowed = false;            // allow skip buttons in station mode
enum_enc_menu     encoderMode = IDLING;                  // Default is IDLING mode
enum_selection    playMode = STATION;                    // Default is STATION mode
#ifdef CHECK_LOOP_TIME
uint32_t          maxLoopTime = 0;                       // just for debugging purposes
#endif

// Needed for the ST7735 display
#include "bluetft.h"                                     // For ILI9163C or ST7735S 128x160 display
void     tftlog(const char *str, uint16_t textColor = (WHITE));

#ifdef ENABLE_DIGITAL_INPUTS
struct progpin_struct                                    // For programmable input pins
{
  int8_t         gpio;                                  // Pin number
  bool           reserved;                              // Reserved for connected devices
  bool           avail;                                 // Pin is available for a command
  String         command;                               // Command to execute when activated
  // Example: "uppreset=1"
  bool           cur;                                   // Current state, true = HIGH, false = LOW
};

progpin_struct   progpin[] =                             // Input pins and programmed function
{
  {  0, false, false,  "", false },
  //{  1, true,  false,  "", false },                    // Reserved for TX Serial output
  {  2, false, false,  "", false },
  //{  3, true,  false,  "", false },                    // Reserved for RX Serial input
  {  4, false, false,  "", false },
  {  5, false, false,  "", false },
  //{  6, true,  false,  "", false },                    // Reserved for FLASH SCK
  //{  7, true,  false,  "", false },                    // Reserved for FLASH D0
  //{  8, true,  false,  "", false },                    // Reserved for FLASH D1
  //{  9, true,  false,  "", false },                    // Reserved for FLASH D2
  //{ 10, true,  false,  "", false },                    // Reserved for FLASH D3
  //{ 11, true,  false,  "", false },                    // Reserved for FLASH CMD
  { 12, false, false,  "", false },
  { 13, false, false,  "", false },
  { 14, false, false,  "", false },
  { 15, false, false,  "", false },
  { 16, false, false,  "", false },
  { 17, false, false,  "", false },
  { 18, false, false,  "", false },                      // Default for SPI CLK
  { 19, false, false,  "", false },                      // Default for SPI MISO
  //{ 20, true,  false,  "", false },                    // Not exposed on DEV board
  { 21, false, false,  "", false },                      // Also Wire SDA
  { 22, false, false,  "", false },                      // Also Wire SCL
  { 23, false, false,  "", false },                      // Default for SPI MOSI
  //{ 24, true,  false,  "", false },                    // Not exposed on DEV board
  { 25, false, false,  "", false },
  { 26, false, false,  "", false },
  { 27, false, false,  "", false },
  //{ 28, true,  false,  "", false },                    // Not exposed on DEV board
  //{ 29, true,  false,  "", false },                    // Not exposed on DEV board
  //{ 30, true,  false,  "", false },                    // Not exposed on DEV board
  //{ 31, true,  false,  "", false },                    // Not exposed on DEV board
  { 32, false, false,  "", false },
  { 33, false, false,  "", false },
  { 34, false, false,  "", false },                      // Note, no internal pull-up
  { 35, false, false,  "", false },                      // Note, no internal pull-up
  { -1, false, false,  "", false }                       // End of list
};

struct touchpin_struct                                   // For programmable input pins
{
  int8_t         gpio;                                   // Pin number GPIO
  bool           reserved;                               // Reserved for connected devices
  bool           avail;                                  // Pin is available for a command
  String         command;                                // Command to execute when activated
  // Example: "uppreset=1"
  bool           cur;                                    // Current state, true = HIGH, false = LOW
  int16_t        count;                                  // Counter number of times low level
};
touchpin_struct   touchpin[] =                           // Touch pins and programmed function
{
  {   4, false, false, "", false, 0 },                   // TOUCH0
  //{ 0, true,  false, "", false, 0 },                   // TOUCH1, reserved for BOOT button
  {   2, false, false, "", false, 0 },                   // TOUCH2
  {  15, false, false, "", false, 0 },                   // TOUCH3
  {  13, false, false, "", false, 0 },                   // TOUCH4
  {  12, false, false, "", false, 0 },                   // TOUCH5
  {  14, false, false, "", false, 0 },                   // TOUCH6
  {  27, false, false, "", false, 0 },                   // TOUCH7
  {  33, false, false, "", false, 0 },                   // TOUCH8
  {  32, false, false, "", false, 0 },                   // TOUCH9
  {  -1, false, false, "", false, 0 }
  // End of table
};
#endif

//**************************************************************************************************
// Pages, CSS and data for the webinterface.                                                       *
//**************************************************************************************************
#include "about_html.h"
#include "config_html.h"
#include "index_html.h"
#include "mp3play_html.h"
#include "radio_css.h"
#include "favicon_ico.h"
#include "defaultprefs.h"

//**************************************************************************************************
// End of global data section.                                                                     *
//**************************************************************************************************

//
//**************************************************************************************************
// VS1053 stuff.  Based on maniacbug library.                                                      *
//**************************************************************************************************
// VS1053 class definition.                                                                        *
// Remark: The VS1053's external clock is 12.288MHz (XTALI set by quarz) and the internal clock    *
//         multiplier will be set to 3.5 which results in an internal clock 43.008 MHz.            *
//         So one internal clock cycle takes 0.02325us (43 clock cycles per us) which is important *
//         for calculating the time it takes to perform a SCI/SDI operation in worst case.         *
//         See chapter 9.6 in the VS1053B datasheet for explanation and more details.              *
//**************************************************************************************************
class VS1053
{
  private:
    int8_t        cs_pin;                        // Pin where CS line is connected
    int8_t        dcs_pin;                       // Pin where DCS line is connected
    int8_t        dreq_pin;                      // Pin where DREQ line is connected
    int8_t        shutdown_pin;                  // Pin where the shutdown line is connected
    uint8_t       curvol;                        // Current volume setting 0..100%
    const uint8_t vs1053_chunk_size = 32;
    // SCI Register                              // max cycles to perform this operation (worst case)
    const uint8_t SCI_MODE          = 0x0;       // 80 CLKI -> 1.86us
    const uint8_t SCI_STATUS        = 0x1;       // 80 CLKI
    const uint8_t SCI_BASS          = 0x2;       // 80 CLKI
    const uint8_t SCI_CLOCKF        = 0x3;       // 1200 XTALI -> 98us
    const uint8_t SCI_AUDATA        = 0x5;       // 450 CLKI -> 10.46us
    const uint8_t SCI_WRAM          = 0x6;       // 100 CLKI -> 2.32us
    const uint8_t SCI_WRAMADDR      = 0x7;       // 100 CLKI
    const uint8_t SCI_AIADDR        = 0xA;       // 210 CLKI -> 4.88us
    const uint8_t SCI_VOL           = 0xB;       // 80 CLKI
    const uint8_t SCI_AICTRL0       = 0xC;       // 80 CLKI
    const uint8_t SCI_AICTRL1       = 0xD;       // 80 CLKI
    const uint8_t SCI_AICTRL2       = 0xE;       // 80 CLKI
    const uint8_t SCI_AICTRL3       = 0xF;       // 80 CLKI
    const uint8_t SCI_num_registers = 0xF;
    // SCI_MODE bits
    const uint8_t SM_SDINEW         = 11;        // Bitnumber in SCI_MODE always on
    const uint8_t SM_RESET          = 2;         // Bitnumber in SCI_MODE soft reset
    const uint8_t SM_CANCEL         = 3;         // Bitnumber in SCI_MODE cancel song
    const uint8_t SM_TESTS          = 5;         // Bitnumber in SCI_MODE for tests
    const uint8_t SM_LINE1          = 14;        // Bitnumber in SCI_MODE for Line input
    // SCI_STATUS bits
    const uint16_t SS_VU_ENABLE     = 0x0200;    // Enables VU-Meter (needs newest patches)
    const uint16_t SS_REFERENCE_SEL = 0x0101;    // Sets higher reference voltage 1.65V instead of 1.3V
    SPISettings   VS1053_SPI;                    // SPI settings for this slave
    uint8_t       endFillByte;                   // Byte to send when stopping song
    bool          okay              = true;      // VS1053 is working

  protected:
    inline void await_data_request(unsigned long maxDelay_us = 0) const
    {
      unsigned long previousTime = micros();

      if (dreq_pin < 0) return;
      while (1) {
        if (digitalRead(dreq_pin) ||             // break when VS1053 is ready for data/next SCI command
            (maxDelay_us > 0 && ((micros() - previousTime) > maxDelay_us))) { // or timeout
          break;
        }  
        NOP();                                   // Very short delay
      }
    }

    inline void control_mode_on() const
    {
      SPI.beginTransaction(VS1053_SPI);          // Prevent other SPI users
      digitalWrite(cs_pin, LOW);
    }

    inline void control_mode_off() const
    {
      digitalWrite(cs_pin, HIGH);                // End control mode
      SPI.endTransaction();                      // Allow other SPI users
    }

    inline void data_mode_on() const
    {
      SPI.beginTransaction(VS1053_SPI);          // Prevent other SPI users
      //digitalWrite(cs_pin, HIGH);              // Bring slave in data mode
      digitalWrite(dcs_pin, LOW);
    }

    inline void data_mode_off() const
    {
      digitalWrite(dcs_pin, HIGH);               // End data mode
      SPI.endTransaction();                      // Allow other SPI users
    }

    // if max delay is 0 then below routines will only return when DREQ is HIGH again !
    uint16_t    read_register(uint8_t _reg, unsigned long maxDelay_us = 0) const;
    void        write_register(uint8_t _reg, uint16_t _value, unsigned long maxDelay_us = 0) const;
    //
    inline bool sdi_send_buffer(uint8_t* data, size_t len);
    void        sdi_send_fillers(size_t length);
    void        wram_write(uint16_t address, uint16_t data);
    uint16_t    wram_read(uint16_t address);

  public:
    // Constructor.  Only sets pin values.  Doesn't touch the chip.  Be sure to call begin()!
    VS1053 (int8_t _cs_pin, int8_t _dcs_pin, int8_t _dreq_pin, int8_t _shutdown_pin);
    void     begin();                                   // Begin operation.  Sets pins correctly,
    // and prepares SPI bus.
    void     startSong();                               // Prepare to start playing. Call this each
    // time a new song starts.
    inline bool playChunk(uint8_t* data,                // Play a chunk of data.  Copies the data to
                          size_t len);                  // the chip.  Blocks until complete.
    // Returns true if more data can be added
    // to fifo
    void     stopSong();                                // Finish playing a song. Call this after
    // the last playChunk call.
    void     setVolume(uint8_t vol);                    // Set the player volume.Level from 0-100,
    // higher is louder.
    void     setTone (uint8_t* rtone);                  // Set the player baas/treble, 4 nibbles for
    // treble gain/freq and bass gain/freq
    inline uint8_t getVolume() const                    // Get the current volume setting.
    { // higher is louder.
      return curvol;
    }
    void     printDetails(const char *header);          // Print config details to serial output
    void     softReset();                               // Do a soft reset
    bool     testComm(const char *header);              // Test communication with module
    inline bool data_request() const
    {
      return (digitalRead(dreq_pin) == HIGH);
    }
#ifdef LOAD_VS1053_PATCH
    void     loadVS1053Patch(void);
#endif
#if defined VU_METER && defined LOAD_VS1053_PATCH
    uint16_t readVuMeter();
#endif
};

//**************************************************************************************************
// VS1053 class implementation.                                                                    *
//**************************************************************************************************

VS1053::VS1053(int8_t _cs_pin, int8_t _dcs_pin, int8_t _dreq_pin, int8_t _shutdown_pin) :
  cs_pin(_cs_pin), dcs_pin(_dcs_pin), dreq_pin(_dreq_pin), shutdown_pin(_shutdown_pin)
{
}

uint16_t VS1053::read_register(uint8_t _reg, unsigned long maxDelay_us) const
{
  uint16_t result;

  control_mode_on();
  SPI.write(3);                                   // Read operation
  SPI.write(_reg);                                // Register to write (0..0xF)
  // Note: transfer16 does not seem to work
  result = (SPI.transfer(0xFF) << 8) |            // Read 16 bits data
           (SPI.transfer(0xFF));
  await_data_request(maxDelay_us);                // Wait for DREQ to be HIGH again or maxDelay_us timeout
  control_mode_off();
  return result;
}

void VS1053::write_register(uint8_t _reg, uint16_t _value, unsigned long maxDelay_us) const
{
  control_mode_on();
  SPI.write(2);                                   // Write operation
  SPI.write(_reg);                                // Register to write (0..0xF)
  SPI.write16(_value);                            // Send 16 bits data
  await_data_request(maxDelay_us);                // Wait for DREQ to be HIGH again or maxDelay_us timeout
  control_mode_off();
}

bool VS1053::sdi_send_buffer(uint8_t* data, size_t len)
{
  size_t chunk_length;                            // Length of chunk 32 byte or shorter

  data_mode_on();
  while (len) {                                   // More to do?
    chunk_length = len;
    if (len > vs1053_chunk_size) {
      chunk_length = vs1053_chunk_size;
    }
    len -= chunk_length;
    await_data_request();                         // Wait for space available
    SPI.writeBytes(data, chunk_length);
    data += chunk_length;
  }
  data_mode_off();
  return data_request();                          // True if more data can de stored in fifo
}

void VS1053::sdi_send_fillers(size_t len)
{
  size_t chunk_length;                            // Length of chunk 32 byte or shorter

  data_mode_on();
  while (len) {                                   // More to do?
    await_data_request();                         // Wait for space available
    chunk_length = len;
    if (len > vs1053_chunk_size) {
      chunk_length = vs1053_chunk_size;
    }
    len -= chunk_length;
    while (chunk_length--) {
      SPI.write(endFillByte);
    }
  }
  data_mode_off();
}

void VS1053::wram_write(uint16_t address, uint16_t data)
{
  write_register(SCI_WRAMADDR, address);
  write_register(SCI_WRAM, data);
}

uint16_t VS1053::wram_read(uint16_t address)
{
  write_register(SCI_WRAMADDR, address);             // Start reading from WRAM
  return read_register(SCI_WRAM);                    // Read back result
}

// write_register() is already defined at this point
#ifdef LOAD_VS1053_PATCH
#include "VS1053_patch.h"
#endif

bool VS1053::testComm(const char *header)
{
  // Test the communication with the VS1053 module.  The result wille be returned.
  // If DREQ is low, there is problably no VS1053 connected.  Pull the line HIGH
  // in order to prevent an endless loop waiting for this signal.  The rest of the
  // software will still work, but readbacks from VS1053 will fail.
  int       i;                                         // Loop control
  uint16_t  r1, r2, cnt = 0;
  uint16_t  delta = 300;                               // 3 for fast SPI

  dbgprint(header);                                    // Show a header
  if (!digitalRead (dreq_pin)) {
    dbgprint("VS1053 not properly installed!(?) DREQ=LOW!");
    // Allow testing without the VS1053 module
    pinMode(dreq_pin,  INPUT_PULLUP);                  // DREQ is now input with pull-up
    return false;                                      // Return bad result
  }
  // Further TESTING.  Check if SCI bus can write and read without errors.
  // We will use the volume setting for this.
  // Will give warnings on serial output if DEBUG is active.
  // A maximum of 20 errors will be reported.
  if (strstr(header, "Fast")) {
    delta = 3;                                         // Fast SPI, more loops
  }
  for (i = 0; (i < 0xFFFF) && (cnt < 20); i += delta) {
    write_register(SCI_VOL, i);                        // Write data to SCI_VOL
    r1 = read_register(SCI_VOL);                       // Read back for the first time
    r2 = read_register(SCI_VOL);                       // Read back a second time
    if  (r1 != r2 || i != r1 || i != r2) {             // Check for 2 equal reads
      dbgprint("VS1053 error retry SB:%04X R1:%04X R2:%04X", i, r1, r2);
      cnt++;
      delay (10);
    }
  }
  okay = (cnt == 0);                                   // True if working correctly
  return (okay);                                       // Return the result
}

void VS1053::begin()
{
  pinMode(dreq_pin, INPUT);                            // DREQ is an input
  pinMode(cs_pin, OUTPUT);                             // the SCI and SDI signals
  pinMode(dcs_pin,OUTPUT);
  digitalWrite(dcs_pin, HIGH);                         // start HIGH for SCI en SDI
  digitalWrite(cs_pin, HIGH);
  if (shutdown_pin >= 0) {                             // shutdown in use?
    pinMode(shutdown_pin, OUTPUT);
    digitalWrite(shutdown_pin, HIGH);                  // shut down audio output
  }
  delay(100);
  // Init SPI in slow mode (200kHz)
  VS1053_SPI = SPISettings(200000, MSBFIRST, SPI_MODE0);
  SPI.setDataMode(SPI_MODE0);
  SPI.setBitOrder(MSBFIRST);
  delay(20);
  if (testComm("Slow SPI, Testing VS1053 read/write registers...")) {
    // GPIO0 & GPIO1 are pulled low with resistors on VS1053 boards from China.
    // Other VS1053 modules may start up in midi mode.  The result is that there is no audio
    // when playing MP3.  You can modify the board, but there is another way:
    //wram_write(0xC017, 3);                           // GPIO DDR = 3
    //wram_write(0xC019, 0);                           // GPIO ODATA = 0
    //
    delay(100);
    softReset();                                       // do a soft reset
#ifdef LOAD_VS1053_PATCH
    dbgprint("VS1053B loading patch %s", PATCH_VERSION); // patch must be loaded >after< reset/sw reset
    delay(20);
    loadVS1053Patch();
    delay(10);
    await_data_request(2000000);                       // wait for DREQ to rise (max 2sec)
#endif    
    // Switch on the analog parts
    write_register(SCI_AUDATA, 44100 + 1);             // 44.1kHz + stereo
    // The next clocksetting allows higher SPI clocking
#if defined VU_METER && defined LOAD_VS1053_PATCH
    // CLKI = XTALI * 3.5, No Multiplier modification allowed, XTALI = 12.288 MHz
    write_register(SCI_CLOCKF, 8 << 12);
#else
    // CLKI = XTALI * 3.0, No Multiplier modification allowed, XTALI = 12.288 MHz
    write_register(SCI_CLOCKF, 6 << 12);
#endif
    delay(10);
    await_data_request(1000000);                       // wait for DREQ to rise (max 1 sec)
    // Now we can set high speed SPI clock.
    VS1053_SPI = SPISettings (5000000, MSBFIRST, SPI_MODE0);   // Speed up SPI
    write_register(SCI_MODE, _BV (SM_SDINEW) | _BV (SM_LINE1));
    testComm("Fast SPI, Testing VS1053 read/write registers again...");
    delay(10);
    await_data_request(1000000);                       // wait for DREQ to rise (max 1sec)
    endFillByte = wram_read(0x1E06) & 0xFF;
    dbgprint("VS1053B endFillByte is %X", endFillByte);
    uint16_t stat = read_register(SCI_STATUS);
    dbgprint("VS1053B Status Register = 0x%04X", stat);
#ifdef LOAD_VS1053_PATCH
    // patch V2.7 is needed to fix SS_REFERENCE_SEL bug 
    if (!(stat & 0x000C)) {
      // Analog power down has been turned off
      dbgprint("VS1053B setting SS_REFERENCE_SEL bit(s) [see VS1053-patches.pdf, Chapter 1.1]");
      write_register(SCI_STATUS, stat | SS_REFERENCE_SEL);
      stat = read_register(SCI_STATUS);
      dbgprint("VS1053B Status Register now = 0x%04X", stat);
    }  
#endif    
#if defined VU_METER && defined LOAD_VS1053_PATCH
    // patch V2.7 is needed to get VU meter feature
    dbgprint("VS1053B setting VU-Meter bit [see VS1053-patches.pdf, Chapter 1.2]");
    write_register(SCI_STATUS, stat | SS_VU_ENABLE);
    stat = read_register(SCI_STATUS);
    dbgprint("VS1053B Status Register now = 0x%04X", stat);
#endif
#ifdef ENABLE_I2S
    // Enabling I2S with MCLK output and sample rate 48kHz 
    wram_write(0xC017, 0x00F0);
    wram_write(0xC040, 0x000C);
    dbgprint("VS1053B I2S interface enabled: MCLK active, Sample Rate = 48kHz");
		const char *p = dbgprint("TOSLINK optical output ok.");
    tftlog(p);
#endif    
    delay(100);
  }
}

void VS1053::setVolume(uint8_t vol)
{
  // Set volume.  Both left and right.
  // Input value is 0..100.  100 is the loudest.
  // Clicking reduced by using 0xf8 to 0x00 as limits.
  uint16_t value;                                      // Value to send to SCI_VOL

  if (vol != curvol) {
    curvol = vol;                                      // Save for later use
    value = map(vol, 0, 100, 0xF8, 0x00);              // 0..100% to one channel
    value = (value << 8) | value;
    write_register(SCI_VOL, value, 3);                 // Volume left and right
    //uint16_t stat = read_register(SCI_STATUS, 3);
    //dbgprint("VS1053B Status Register = 0x%04X", stat);
    //write_register(SCI_STATUS, stat | 0x0001, 3);    // shows no effect! (Chapter 9.6.2 in datasheet)
  }
}

void VS1053::setTone(uint8_t *rtone)                   // Set bass/treble (4 nibbles)
{
  // Set tone characteristics.  See documentation for the 4 nibbles.
  uint16_t value = 0;                                  // Value to send to SCI_BASS
  int      i;                                          // Loop control

  for (i = 0; i < 4; i++) {
    value = (value << 4) | rtone[i];                   // Shift next nibble in
  }
  write_register(SCI_BASS, value, 3);
}

void VS1053::startSong()
{
  sdi_send_fillers (10);
  if (shutdown_pin >= 0) {                             // Shutdown in use?
    digitalWrite(shutdown_pin, LOW);                   // Enable audio output
  }

}

bool VS1053::playChunk(uint8_t* data, size_t len)
{
  return okay && sdi_send_buffer(data, len);           // True if more data can be added to fifo
}

void VS1053::stopSong()
{
  uint16_t modereg;                                    // Read from mode register
  int      i;                                          // Loop control

  sdi_send_fillers(2052);
  if (shutdown_pin >= 0) {                             // Shutdown in use?
    digitalWrite(shutdown_pin, HIGH);                  // Disable audio output
  }
  delay(10);
  write_register(SCI_MODE, _BV (SM_SDINEW) | _BV (SM_CANCEL), 3);
  for (i = 0; i < 200; i++) {
    sdi_send_fillers(32);
    modereg = read_register(SCI_MODE, 3);              // Read status
    if ((modereg & _BV (SM_CANCEL)) == 0) {
      sdi_send_fillers(2052);
      //dbgprint("Song stopped correctly after %d msec", i * 10);
      return;
    }
    delay(10);
  }
  printDetails("Song stopped incorrectly!");
}

void VS1053::softReset()
{
  write_register(SCI_MODE, _BV (SM_SDINEW) | _BV (SM_RESET), 3);
  delay(10);
  await_data_request();
}

void VS1053::printDetails(const char *header)
{
  uint16_t regbuf[16];
  uint8_t  i;

  dbgprint(header);
  dbgprint("REG   Contents");
  dbgprint("---   -----");
  for (i = 0; i <= SCI_num_registers; i++) {
    regbuf[i] = read_register(i);
  }
  for (i = 0; i <= SCI_num_registers; i++) {
    delay(5);
    dbgprint("%3X - %5X", i, regbuf[i]);
  }
}

#if defined VU_METER && defined LOAD_VS1053_PATCH
uint16_t VS1053::readVuMeter()
{
  return okay ? read_register(SCI_AICTRL3, 3) : 0;         // Read back VU-Meter result
}
#endif

// The object for the MP3 player
VS1053* vs1053player;

//**************************************************************************************************
// End of VS1053 stuff.                                                                            *
//**************************************************************************************************


//**************************************************************************************************
//                                      N V S O P E N                                              *
//**************************************************************************************************
// Open Preferences with my-app namespace. Each application module, library, etc.                  *
// has to use namespace name to prevent key name collisions. We will open storage in               *
// RW-mode (second parameter has to be false).                                                     *
//**************************************************************************************************
void nvsopen()
{
  if (!nvshandle) {                                       // Opened already?
    nvserr = nvs_open(NAME, NVS_READWRITE, &nvshandle);   // No, open nvs
    if (nvserr) {
      dbgprint("nvs_open failed!");
    }
  }
}

//**************************************************************************************************
//                                      N V S C L E A R                                            *
//**************************************************************************************************
// Clear all preferences.                                                                          *
//**************************************************************************************************
esp_err_t nvsclear()
{
  nvsopen();                                         // Be sure to open nvs
  return nvs_erase_all(nvshandle);                   // Clear all keys
}

//**************************************************************************************************
//                                      N V S G E T S T R                                          *
//**************************************************************************************************
// Read a string from nvs.                                                                         *
//**************************************************************************************************
String nvsgetstr(const char* key)
{
  static char nvs_buf[NVSBUFSIZE];         // Buffer for contents
  size_t      len = NVSBUFSIZE;            // Max length of the string, later real length

  nvsopen();                               // Be sure to open nvs
  nvs_buf[0] = '\0';                       // Return empty string on error
  nvserr = nvs_get_str(nvshandle, key, nvs_buf, &len);
  if (nvserr) {
    dbgprint("nvs_get_str failed %X for key %s, keylen is %d, len is %d!",
               nvserr, key, strlen (key), len);
    dbgprint("Contents: %s", nvs_buf);
  }
  return String(nvs_buf);
}

//**************************************************************************************************
//                                      N V S S E T S T R                                          *
//**************************************************************************************************
// Put a key/value pair in nvs.  Length is limited to allow easy read-back.                        *
// Max key lenght is 15 chars (defined in nvs.h) !!!!!! No writing if no change.                   *
//**************************************************************************************************
esp_err_t nvssetstr(const char* key, String val)
{
  String curcont;                                          // Current contents
  bool   wflag = true;                                     // Assume update or new key

  //dbgprint("Setstring for %s: %s", key, val.c_str());
  if (val.length() >= NVSBUFSIZE) {                        // Limit length of string to store
    dbgprint("nvssetstr length failed!");
    return ESP_ERR_NVS_NOT_ENOUGH_SPACE;
  }
  if (nvsSearch(key)) {                                    // Already in nvs?
    curcont = nvsgetstr(key);                              // Read current value
    wflag = (curcont != val);                              // Value change?
  }
  if (wflag) {                                             // Update or new?
    //dbgprint("nvssetstr update value");
    nvserr = nvs_set_str(nvshandle, key, val.c_str());     // Store key and value
    if (nvserr) {                                          // Check error
      dbgprint("nvssetstr failed!");
    }
    else {
      dbgprint("nvssetstr: %s = %s saved to NVS flash", key, val.c_str());
    }
  }
  return nvserr;
}

//**************************************************************************************************
//                                      N V S C H K E Y                                            *
//**************************************************************************************************
// Change a keyname in in nvs.                                                                     *
//**************************************************************************************************
void nvschkey (const char* oldk, const char* newk)
{
  String curcont;                                     // Current contents

  if (nvsSearch(oldk)) {                              // Old key in nvs?
    curcont = nvsgetstr(oldk);                        // Read current value
    nvs_erase_key(nvshandle, oldk);                   // Remove key
    nvssetstr(newk, curcont);                         // Insert new
  }
}

//**************************************************************************************************
//                                      C L A I M S P I                                            *
//**************************************************************************************************
// Claim the SPI bus.  Uses FreeRTOS semaphores.                                                   *
//**************************************************************************************************
void claimSPI(const char* p)
{
  const TickType_t ctry = 10;                         // Time to wait for semaphore (10ms)

  while (xSemaphoreTake(SPIsem, ctry) != pdTRUE) {    // claim SPI bus
    //...
  }
}

//**************************************************************************************************
//                                   R E L E A S E S P I                                           *
//**************************************************************************************************
// Free the SPI bus.  Uses FreeRTOS semaphores.                                                    *
//**************************************************************************************************
void releaseSPI()
{
  xSemaphoreGive(SPIsem);                               // release SPI bus
}

//**************************************************************************************************
//                                      Q U E U E F U N C                                          *
//**************************************************************************************************
// Queue a special function for the play task.                                                     *
//**************************************************************************************************
void queuefunc(int func)
{
  qdata_struct specchunk;                              // Special function to queue

  specchunk.datatyp = func;                            // Put function in datatyp
  xQueueSend(dataQueue, &specchunk, 200);              // Send to queue
}

//**************************************************************************************************
//                                      N V S S E A R C H                                          *
//**************************************************************************************************
// Check if key exists in nvs.                                                                     *
//**************************************************************************************************
bool nvsSearch(const char* key)
{
  size_t len = NVSBUFSIZE;                              // Length of the string

  nvsopen();                                            // Be sure to open nvs
  nvserr = nvs_get_str(nvshandle, key, NULL, &len);     // Get length of contents
  return (nvserr == ESP_OK);                            // Return true if found
}

//**************************************************************************************************
//                                      T F T S E T                                                *
//**************************************************************************************************
// Request to display a segment on TFT.  Version for char* and String parameter.                   *
//**************************************************************************************************
void tftset(uint16_t inx, const char *str)
{
  if (inx < TFTSECS) {                                 // segment available on display ?
    if (str) {                                         // string specified?
      tftdata[inx].str = String(str);                  // set string
    }
    tftdata[inx].update_req = true;                    // and request update
  }
}

void tftset(uint16_t inx, String& str)
{
  tftdata[inx].str = str;                              // set string
  tftdata[inx].update_req = true;                      // and request update
}

//**************************************************************************************************
//                                      U T F 8 A S C I I                                          *
//**************************************************************************************************
// UTF8-Decoder: convert UTF8-string to extended ASCII.                                            *
// Convert a single Character from UTF8 to Extended ASCII.                                         *
// Return "0" if a byte has to be ignored.                                                         *
//**************************************************************************************************
byte utf8ascii(byte ascii)
{
  static const byte lut_C3[] = { "AAAAAAACEEEEIIIIDNOOOOO#0UUUU##Baaaaaaaceeeeiiiidnooooo##uuuuyyy" };
  static byte       c1;              // Last character buffer
  byte              res = 0;         // Result, default 0

  if (ascii <= 0x7F) {               // Standard ASCII-set 0..0x7F handling
    c1 = 0;  res = ascii;            // Return unmodified
  }
  else if ((c1 != 0xC3) && (ascii == 0xC9)) {
    c1 = 0;  res = 'E';              // É
  }
  else if ((c1 != 0xC3) && (ascii == 0x84 || ascii == 0x86 || ascii == 0xE0 || ascii == 0xE1 || ascii == 0xE4 || ascii == 0xE5)) {
    c1 = 0;  res = 'a';              // à, á, å oder ä
  }
  else if ((c1 != 0xC3) && (ascii == 0xE7)) {
    c1 = 0;  res = 'c';              // ç
  }
  else if ((c1 != 0xC3) && (ascii == 0x82 || ascii == 0xD9 || ascii == 0xE9 || ascii == 0xEB)) {
    c1 = 0;  res = 'e';              // é, ë
  }
  else if ((c1 != 0xC3) && (ascii == 0xED)) {
    c1 = 0;  res = 'i';              // í
  }
  else if ((c1 != 0xC3) && (ascii == 0xDF)) {
    c1 = 0;  res = 'B';              // ß
  }
  else if ((c1 != 0xC3) && (ascii == 0x94 || ascii == 0xF6)) {
    c1 = 0;  res = 'o';              // ö
  }
  else if ((c1 != 0xC3) && (ascii == 0x81 || ascii == 0xFC)) {
    c1 = 0;  res = 'u';              // ü
  }
  else if ((c1 != 0xC3) && (ascii == 0x8E || ascii == 0xC4)) {
    c1 = 0;  res = 'A';              // Ä
  }
  else if ((c1 != 0xC3) && (ascii == 0x99 || ascii == 0xD6)) {
    c1 = 0;  res = 'O';              // Ö
  }
  else if ((c1 != 0xC3) && (ascii == 0x9A || ascii == 0xDC)) {
    c1 = 0;  res = 'U';              // Ü
  }
  else if ((c1 != 0xC3) && (ascii == 0xB4 || ascii == 0xEF)) {
    c1 = 0;  res = '\'';             // ´
  }
  else {
    switch (c1) {                    // conversion depending on first UTF8-character
      case 0x00: c1 = ascii;         // remember first special character
                 break;              // return zero, character has to be ignored
      case 0xC2: if (ascii == 0xB7) res = '-';
                 else res = '~';
                 c1 = 0;
                 break;
      case 0xC3: res = lut_C3[ascii - 128];
                 c1 = 0;
                 break;
      case 0x82: if (ascii == 0xAC) {
                   res = 'E';        // special case Euro-symbol
                 }
                 c1 = 0;
                 break;
    }
  }
  if (ascii > 0x7F) dbgprint("utf8ascii() ---> Special Char: 0x%02X, return: 0x%02X", ascii, res);

  return res;                        
}

//**************************************************************************************************
//                                      U T F 8 A S C I I                                          *
//**************************************************************************************************
// In Place conversion UTF8-string to Extended ASCII (ASCII is shorter!).                          *
//**************************************************************************************************
void utf8ascii(char *s)
{
  int  i, k = 0;                     // Indexes for in en out string
  char c;

  for (i = 0; s[i]; i++) {           // For every input character
    c = utf8ascii(s[i]);             // Translate if necessary
    if (c) {                         // Good translation?
      s[k++] = c;                    // Yes, put in output string
    }
  }
  s[k] = 0;                          // Take care of delimeter
}

//**************************************************************************************************
//                                      U T F 8 A S C I I                                          *
//**************************************************************************************************
// Conversion UTF8-String to Extended ASCII String.                                                *
//**************************************************************************************************
String utf8ascii(const char *s)
{
  int  len = strlen(s);
  char buf[len + 1];
  
  strncpy(buf, s, sizeof(buf));
  utf8ascii(buf);

  return String(buf);
}

//**************************************************************************************************
//                                      U T F 16 A S C I I                                         *
//**************************************************************************************************
// For encoding ID3-Tags                                                                           *
//**************************************************************************************************
void utf16ascii(char *s, int length)
{
  int  i, k = 0;

  if (s[0] == 0xFF && s[1] == 0xFE) {       // Little Endian
    i = 2;
  }
  else if (s[0] == 0xFE && s[1] == 0xFF) {  // Big Endian
    i = 3;
  }
  else {
    //dbgprint("utf16ascii: ID3-Tag UTF16-Format not recognized 0x%02x 0x%02x", s[0], s[1]);
    return;
  }
  for (; i < length;) {
    s[k++] = s[i];                          // put in output string
    i += 2;
  }
  s[k] = 0;                                 // Take care of delimeter
}

//**************************************************************************************************
//                                          D B G P R I N T                                        *
//**************************************************************************************************
// Send a line of info to serial output.  Works like vsprintf(), but checks the DEBUG flag.        *
// Print only if DEBUG flag is true.  Always returns the formatted string.                         *
//**************************************************************************************************
char* dbgprint(const char* format, ...)
{
  static char sbuf[DEBUG_BUFFER_SIZE];                 // For debug lines
  va_list varArgs;                                     // For variable number of params

  va_start(varArgs, format);                           // Prepare parameters
  vsnprintf(sbuf, sizeof(sbuf), format, varArgs);      // Format the message
  va_end(varArgs);                                     // End of using parameters
  if (DEBUG) {                                         // DEBUG on?
    Serial.print("D: ");                               // Yes, print prefix
    Serial.println(sbuf);                              // and the info
#ifdef PORT23_ACTIVE
    if (dbgConnectFlag) {
      _claimSPI("dbg1");                               // claim SPI bus
      uint8_t erg = dbgclient.connected();
      _releaseSPI();                                   // release SPI bus
      if (erg) {                                       // just to make sure the client is still connected
        char sbuf1[DEBUG_BUFFER_SIZE + 5];
        snprintf(sbuf1, sizeof(sbuf1), "D: %s\r\n", sbuf); 
        size_t len = strlen(sbuf1);
        _claimSPI("dbg2");                             // claim SPI bus
        dbgclient.write(sbuf1, len);
        _releaseSPI();                                 // release SPI bus
      }
      else {
        dbgConnectFlag = false;                        // clear the flag
      }
    }
#endif
  }
  return sbuf;                                         // Return stored string
}
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
void loop()
{
  //delay(1);                                             // resets task switcher watchdog, just in case it's needed
#ifdef ENABLE_ESP32_HW_WDT
  esp_task_wdt_reset();                                 // avoid panic and subsequent ESP32 restart
#endif   
#ifdef CHECK_LOOP_TIME
  uint32_t timing;                                      // for calculation of loop() round times
  timing = millis();
#endif
  mp3loop();                                            // Do mp3 related actions
  if (resetreq) {                                       // Reset requested?
    delay(1000);                                        // Yes, wait some time
    ESP.restart();                                      // Reboot
  }
  scanserial();                                         // Handle serial input
#ifdef ENABLE_DIGITAL_INPUTS  
  scandigital();                                        // Scan digital inputs
#endif  
#ifdef ENABLE_INFRARED
  scanIR();                                             // See if IR input
#endif
#ifndef USE_ETHERNET
  ArduinoOTA.handle();                                  // Check for OTA
#endif
  mp3loop();                                            // Do more mp3 related actions
#if defined(ENABLE_CMDSERVER) && !defined(PORT23_ACTIVE)
  handlehttpreply();
  _claimSPI("loop");                                    // claim SPI bus
  cmdclient = cmdserver.available();                    // Check Input from client
  _releaseSPI();                                        // release SPI bus
  if (cmdclient) {                                      // Client connected ?
    dbgprint("loop(): command client available");
    handlehttp();
  }
#endif  
  //
  handleSaveReq();                                      // See if time to save settings
  checkEncoderAndButtons();                             // check rotary encoder & button functions
#ifdef PORT23_ACTIVE
  handleClientOnPort23();                               // check possible debug client requests
#endif
#ifdef CHECK_LOOP_TIME
  timing = millis() - timing;
  if (timing > maxLoopTime) {                           // new maximum found?
    maxLoopTime = timing;                               // yes, set new maximum
    dbgprint("Max duration loop() = %d ms", timing);    // and report it
  }
#endif
}

//**************************************************************************************************
//                                    C H K H D R L I N E                                          *
//**************************************************************************************************
// Check if a line in the header is a reasonable headerline.                                       *
// Normally it should contain something like "icy-xxxx:abcdef".                                    *
//**************************************************************************************************
bool chkhdrline(const char* str)
{
  char b;                                             // Byte examined
  int  len = 0;                                       // Length of string

  while ((b = *str++)) {                              // Search to end of string
    len++;                                            // Update string length
    if (!isalpha(b)) {                                // Alpha (a-z, A-Z)
      if (b != '-') {                                 // Minus sign is allowed
        if (b == ':') {                               // Found a colon?
          return ((len > 5) && (len < 50));           // Yes, okay if length is okay
        }
        else {
          return false;                               // Not a legal character
        }
      }
    }
  }
  return false;                                       // End of string without colon
}

//**************************************************************************************************
//                            S C A N _ C O N T E N T _ L E N G T H                                *
//**************************************************************************************************
// If the line contains content-length information: set clength (content length counter).          *
//**************************************************************************************************
void scan_content_length(const char* metalinebf)
{
  if (strstr(metalinebf, "Content-Length")) {        // Line contains content length
    clength = atoi(metalinebf + 15);                 // Yes, set clength
    dbgprint("Content-Length is %d", clength);       // Show for debugging purposes
  }
}

//**************************************************************************************************
//                                   H A N D L E B Y T E _ C H                                     *
//**************************************************************************************************
// Handle the next byte of data from server or mp3 file.                                           *
// Chunked transfer encoding aware. Chunk extensions are not supported.                            *
//**************************************************************************************************
void handlebyte_ch(uint8_t b)
{
  static int       chunksize = 0;                      // Chunkcount read from stream
  static uint16_t  playlistcnt;                        // Counter to find right entry in playlist
  static int       LFcount;                            // Detection of end of header
  static bool      ctseen = false;                     // First line of header seen or not
  static bool      nameseen = false;                   // Name of station seen
  static bool      brseen = false;                     // Bitrate of station seen

  if (chunked &&
       (dataMode & (DATA |                             // Test op DATA handling
                    METADATA |
                    PLAYLISTDATA))) {
    if (chunkcount == 0) {                             // Expecting a new chunkcount?
      if (b == '\r') {                                 // Skip CR
        return;
      }
      else if (b == '\n') {                            // LF ?
        chunkcount = chunksize;                        // Yes, set new count
        chunksize = 0;                                 // For next decode
        return;
      }
      // We have received a hexadecimal character.  Decode it and add to the result.
      b = toupper(b) - '0';                            // Be sure we have uppercase
      if (b > 9) {
        b = b - 7;                                     // Translate A..F to 10..15
      }
      chunksize = (chunksize << 4) + b;
      return;
    }
    chunkcount--;                                      // Update count to next chunksize block
  }
  if (dataMode == DATA) {                              // Handle next byte of MP3/Ogg data
    *outqp++ = b;
    if (outqp == (outchunk.buf + sizeof(outchunk.buf))) { // Buffer full?
      outchunk.datatyp = QDATA;                        // This chunk dedicated to QDATA
      // Send data to playTask queue.  If the buffer cannot be placed within 200 ticks,
      // the queue is full, while the sender tries to send more.  The chunk will be dis-
      // carded in that case.
      xQueueSend(dataQueue, &outchunk, 200);           // send to queue (wait max 200 ticks [resp. 200ms])
      outqp = outchunk.buf;                            // item empty now
    }
    //*/
    if (metaint) {                                     // No METADATA on Ogg streams or mp3 files
      if (--datacount == 0) {                          // End of datablock?
        dataMode = METADATA;
        metalinebfx = -1;                              // Expecting first metabyte (counter)
      }
    }
    return;
  }
  if (dataMode == INIT) {                              // Initialize for header receive
    ctseen = false;                                    // Contents type not seen yet
    nameseen = false;                                  // Name of station not seen yet
    brseen = false;                                    // Bitrate of station not seen yet
    metaint = 0;                                       // No metaint found
    LFcount = 0;                                       // For detection end of header
    bitrate = 0;                                       // Bitrate still unknown
    dbgprint("Switch to HEADER"); 
    dataMode = HEADER;                                 // Handle header
    totalCount = 0;                                    // Reset totalCount
    metalinebfx = 0;                                   // No metadata yet
    metalinebf[0] = '\0';
    muteFlag = 16;                                     // ca. 1,6 sek.
  }
  if (dataMode == HEADER) {                            // Handle next byte of MP3 header
    b = utf8ascii(b);
    if ((b > 0x7F) ||                                  // Ignore unprintable characters
        (b == '\r') ||                                 // Ignore CR
        (b == '\0')) {                                 // Ignore NULL
      // Yes, ignore
    }
    else if (b == '\n') {                              // Linefeed ?
      LFcount++;                                       // Count linefeeds
      metalinebf[metalinebfx] = '\0';                  // Take care of delimiter
      if (chkhdrline(metalinebf)) {                    // Reasonable input?
        dbgprint("Headerline: %s", metalinebf);        // Show headerline
        String metaline = String(metalinebf);          // Convert to string
        String lcml = metaline;                        // Use lower case for compare
        lcml.toLowerCase();
        if (lcml.startsWith("location: http://")) {    // Redirection?
          host = metaline.substring(17);               // Yes, get new URL
          hostreq = true;                              // And request this one
          dbgprint("Redirection to new host");
        }
        else if (lcml.indexOf("content-type") == 0) {  // Line beginning with "Content-Type: xxxx/yyy"
          ctseen = true;                               // Yes, remember seeing this
          //String ct = metaline.substring(13);        // Set contentstype. Not used yet
          //ct.trim();
          //dbgprint("%s seen.", ct.c_str());
        }
        else if (lcml.startsWith("icy-br:")) {
          brseen = true;
          bitrate = metaline.substring(7).toInt();     // Found bitrate tag, read the bitrate
          if (bitrate == 0) {                          // For Ogg br is like "Quality 2"
            bitrate = 87;                              // Dummy bitrate
          }
        }
        else if (lcml.startsWith("icy-metaint:")) {
          metaint = metaline.substring(12).toInt();    // Found metaint tag, read the value
        }
        else if (lcml.startsWith("icy-name:")) {
          icyname = metaline.substring(9);             // Get station name
          icyname.trim();                              // Remove leading and trailing spaces
          if (icyname.length() > 0) {
            nameseen = true;
            if (icyname.length() > 62) {               // line limiting
              icyname.remove(59);
              icyname += "...";
            }
          }
        }
        else if (lcml.startsWith("transfer-encoding:")) {
          // Station provides chunked transfer
          if (lcml.endsWith("chunked")) {
            chunked = true;                            // Remember chunked transfer mode
            chunkcount = 0;                            // Expect chunkcount in DATA
          }
        }
      }
      metalinebfx = 0;                                 // Reset this line
      if ((LFcount == 2) && ctseen) {                  // Content type seen and a double LF?
        dbgprint("Switch to DATA, bitrate is %dkbps"   // Show bitrate
                 ", metaint is %d", bitrate, metaint); // and metaint
        dataMode = DATA;                               // Expecting data now
        datacount = metaint;                           // Number of bytes before first metadata
        skipStationAllowed = true;                     // now allow skip buttons in station mode
        if (!nameseen) {                               // no name seen, that's highly unusual
          // so we try to find it in the preset list
          String tmp;
          int8_t inx;

          icyname = host;                              // by default display host instead of station name
          if (icyname.length() > 62) {                 // line limiting
            icyname.remove(59);
            icyname += "...";
          }
          //nameseen = true;

          dbgprint("No icy-name! Search name for host \"%s\" in presets", host.c_str());
          for (int i = 0; i <= 99; i++) {
            tmp = readhostfrompref(i);                 // Get host spec and possible comment
            if (tmp == "") {                           // End of presets?
              dbgprint("No preset for this host found! Index which breaked = %d.", i);
              break;                                   // no matching entry found
            }
            if (tmp.indexOf(host) >= 0) {              // Found host in preset ?
              dbgprint("Found host in preset %d.", i);
              inx = tmp.indexOf("#");                  // Get position of "#"
              if (inx > 0) {                           // Hash sign present?
                tmp.remove(0, inx + 1);            // Yes, remove non-comment part
                chomp(tmp);                        // Remove garbage from description
                tmp.trim();                           // Remove leading & trailing whitespace
                if (tmp.length() > 0) {                // Something left ?
                  inx = tmp.indexOf(" - ");
                  if (inx >= 0) {
                    tmp.remove(0, inx + 3);
                  }
                  dbgprint("Name found = \"%s\"", tmp.c_str());
                  icyname = tmp;
                }
              }
              break;
            }
          }
        }
        if (brseen) {
          icyname += " (" + String(bitrate) + "kbps)";
        }
        tftset(1, "...waiting for text...");           // Set screen segment middle part
        tftset(3, icyname);                            // Set screen segment bottom part
        lastAlbumStation = icyname;
        queuefunc(QSTARTSONG);                         // Queue a request to start song
      }
    }
    else {
      metalinebf[metalinebfx++] = (char)b;             // Normal character, put new char in metaline
      if (metalinebfx >= METASIZ) {                    // Prevent overflow
        metalinebfx--;
      }
      LFcount = 0;                                     // Reset double CRLF detection
    }
    return;
  }
  if (dataMode == METADATA) {                          // Handle next byte of metadata
    if (metalinebfx < 0) {                             // First byte of metadata?
      metalinebfx = 0;                                 // Prepare to store first character
      metacount = b * 16 + 1;                          // New count for metadata including length byte
    }
    else {
      metalinebf[metalinebfx++] = (char)b;             // Normal character, put new char in metaline
      if (metalinebfx >= METASIZ) {                    // Prevent overflow
        metalinebfx--;
      }
    }
    if (--metacount == 0) {
      metalinebf[metalinebfx] = '\0';                  // Make sure line is limited
      if (strlen(metalinebf)) {                        // Any info present?
        // metaline contains artist and song name.  For example:
        // "StreamTitle='Don McLean - American Pie';StreamUrl='';"
        // Sometimes it is just other info like:
        // "StreamTitle='60s 03 05 Magic60s';StreamUrl='';"
        // Isolate the StreamTitle, remove leading and trailing quotes if present.
        showStreamTitle(metalinebf);                   // Show artist and title if present in metadata
      }
      if (metalinebfx > (METASIZ - 10)) {              // Unlikely metaline length?
        dbgprint("Metadata block too long! Skipping all Metadata from now on.");
        metaint = 0;                                   // Probably no metadata or network problem
      }
      datacount = metaint;                             // Reset data count
      //bufcnt = 0;                                    // Reset buffer count
      dataMode = DATA;                                 // Expecting data
    }
  }
  if (dataMode == PLAYLISTINIT) {                      // Initialize for receive .m3u file
    // We are going to use metadata to read the lines from the .m3u file
    // Sometimes this will only contain a single line
    metalinebfx = 0;                                   // Prepare for new line
    LFcount = 0;                                       // For detection end of header
    dataMode = PLAYLISTHEADER;                         // Handle playlist data
    playlistcnt = 1;                                   // Reset for compare
    totalCount = 0;                                    // Reset totalCount
    clength = 0xFFFF;                                  // Content-length unknown
    dbgprint("Read from playlist");
  }
  if (dataMode == PLAYLISTHEADER) {                    // Read header
    if ((b > 0x7F) ||                                  // Ignore unprintable characters
        (b == '\r') ||                                 // Ignore CR
        (b == '\0')) {                                 // Ignore NULL
      return;                                          // Quick return
    }
    else if (b == '\n') {                              // Linefeed ?
      LFcount++;                                       // Count linefeeds
      metalinebf[metalinebfx] = '\0';                  // Take care of delimeter
      dbgprint("Playlistheader: %s", metalinebf);      // Show playlistheader
      scan_content_length(metalinebf);                 // Check if it is a content-length line
      metalinebfx = 0;                                 // Ready for next line
      if (LFcount == 2) {
        dbgprint("Switch to PLAYLISTDATA, "            // For debug
                 "search for entry %d", playlist_num);
        dataMode = PLAYLISTDATA;                       // Expecting data now
        return;
      }
    }
    else {
      metalinebf[metalinebfx++] = (char)b;             // Normal character, put new char in metaline
      if (metalinebfx >= METASIZ) {                    // Prevent overflow
        metalinebfx--;
      }
      LFcount = 0;                                     // Reset double CRLF detection
    }
  }
  if (dataMode == PLAYLISTDATA) {                      // Read next byte of .m3u file data
    clength--;                                         // Decrease content length by 1
    if ((b > 0x7F) ||                                  // Ignore unprintable characters
        (b == '\r') ||                                 // Ignore CR
        (b == '\0')) {                                 // Ignore NULL
      // Yes, ignore
    }
    if (b != '\n') {                                   // Linefeed?
      // No, normal character in playlistdata,
      metalinebf[metalinebfx++] = (char)b;             // add it to metaline
      if (metalinebfx >= METASIZ) {                    // Prevent overflow
        metalinebfx--;
      }
    }
    if ((b == '\n') ||                                 // linefeed ?
         (clength == 0)) {                             // Or end of playlist data contents
      int inx;                                         // Pointer in metaline
      metalinebf[metalinebfx] = '\0';                  // Take care of delimeter
      dbgprint("Playlistdata: %s", metalinebf);        // Show playlistheader
      if (strlen(metalinebf) < 5) {                    // Skip short lines
        metalinebfx = 0;                               // Flush line
        metalinebf[0] = '\0';
        return;
      }
      String metaline = String(metalinebf);            // Convert to string
      if (metaline.indexOf("#EXTINF:") >= 0) {         // Info?
        if (playlist_num == playlistcnt) {             // Info for this entry?
          inx = metaline.indexOf(",");                 // Comma in this line?
          if (inx > 0) {
            // Show artist and title if present in metadata
            showStreamTitle(metaline.substring(inx + 1).c_str(), true);
          }
        }
      }
      if (metaline.startsWith("#")) {                  // Commentline?
        metalinebfx = 0;                               // Yes, ignore
        return;                                        // Ignore commentlines
      }
      // Now we have an URL for a .mp3 file or stream.  Is it the rigth one?
      dbgprint("Entry %d in playlist found: %s", playlistcnt, metalinebf);
      if (playlist_num == playlistcnt) {
        inx = metaline.indexOf("http://");             // Search for "http://"
        if (inx >= 0) {                                // Does URL contain "http://"?
          host = metaline.substring(inx + 7);          // Yes, remove it and set host
        }
        else {
          host = metaline;                             // Yes, set new host
        }
        connectToHost();                               // Connect to it
      }
      metalinebfx = 0;                                 // Prepare for next line
      host = playlist;                                 // Back to the .m3u host
      playlistcnt++;                                   // Next entry in playlist
    }
  }
}

#if defined(ENABLE_CMDSERVER) && !defined(PORT23_ACTIVE)
//**************************************************************************************************
//                                     G E T C O N T E N T T Y P E                                 *
//**************************************************************************************************
// Returns the contenttype of a file to send.                                                      *
//**************************************************************************************************
String getContentType(String filename)
{
  if      (filename.endsWith(".html")) return "text/html";
  else if (filename.endsWith(".png"))  return "image/png";
  else if (filename.endsWith(".gif"))  return "image/gif";
  else if (filename.endsWith(".jpg"))  return "image/jpeg";
  else if (filename.endsWith(".ico"))  return "image/x-icon";
  else if (filename.endsWith(".css"))  return "text/css";
  else if (filename.endsWith(".zip"))  return "application/x-zip";
  else if (filename.endsWith(".gz"))   return "application/x-gzip";
  else if (filename.endsWith(".mp3"))  return "audio/mpeg";
  else if (filename.endsWith(".pw"))   return "";        // Passwords are secret
  return "text/plain";
}

//**************************************************************************************************
//                                        H A N D L E F S F                                        *
//**************************************************************************************************
// Handling of requesting pages from the PROGMEM. Example: favicon.ico                             *
//**************************************************************************************************
void handleFSf(const String& pagename)
{
  String      ct;                                    // Content type
  const char* p;
  int         l;                                     // Size of requested page
  int         TCPCHUNKSIZE = 1024;                   // Max number of bytes per write

  dbgprint("FileRequest received %s", pagename.c_str());
  ct = getContentType(pagename);                     // Get content type
  if ((ct == "") || (pagename == "")) {              // Empty is illegal
    _claimSPI("handlefsf1");                         // claim SPI bus
    cmdclient.println("HTTP/1.1 404 Not Found");
    cmdclient.println("");
//#ifdef USE_ETHERNET
//    cmdclient.flush();                             // not needed in the end
//    cmdclient.stop();
//#endif
    _releaseSPI();                                   // release SPI bus
    return;
  }
  else {
    if (pagename.indexOf("index.html") >= 0) {       // Index page is in PROGMEM
      p = index_html;
      l = sizeof(index_html);
    }
    else if (pagename.indexOf("radio.css") >= 0) {   // CSS file is in PROGMEM
      p = radio_css + 1;
      l = sizeof(radio_css);
    }
    else if (pagename.indexOf("config.html") >= 0) { // Config page is in PROGMEM
      p = config_html;
      l = sizeof(config_html);
    }
    else if (pagename.indexOf("mp3play.html") >= 0) {// Mp3player page is in PROGMEM
      p = mp3play_html;
      l = sizeof(mp3play_html);
    }
    else if (pagename.indexOf("about.html") >= 0) {  // About page is in PROGMEM
      p = about_html;
      l = sizeof(about_html);
    }
    else if (pagename.indexOf("favicon.ico") >= 0) { // Favicon icon is in PROGMEM
      p = (char*)favicon_ico;
      l = sizeof(favicon_ico);
    }
    else {
      p = index_html;
      l = sizeof(index_html);
    }
    if (*p == '\n') {                                // If page starts with newline:
      p++;                                           // Skip first character
      l--;
    }
    dbgprint("Length of page is %d", strlen (p));
    _claimSPI("handlefsf2");                        // claim SPI bus
    cmdclient.print(httpHeader(ct));                // Send header
    _releaseSPI();                                  // release SPI bus
    // The content of the HTTP response follows the header:
    if (l < 10) {
      _claimSPI("handlefsf3");                      // claim SPI bus
      cmdclient.println ("Testline<br>");
      _releaseSPI();                                // release SPI bus
    }
    else {
      while (l) {                                   // Loop through the output page
        if (l <= TCPCHUNKSIZE) {                    // Near the end?
          _claimSPI("handlefsf4");                  // claim SPI bus
          cmdclient.write(p, l);                    // Yes, send last part
          _releaseSPI();                            // release SPI bus
          l = 0;
        }
        else {
          _claimSPI("handlefsf5");                  // claim SPI bus
          cmdclient.write(p, TCPCHUNKSIZE);         // Send part of the page
          _releaseSPI();                            // release SPI bus
          p += TCPCHUNKSIZE;                        // Update startpoint and rest of bytes
          l -= TCPCHUNKSIZE;
        }
      }
    }
    // The HTTP response ends with another blank line:
    _claimSPI("handlefsf6");                        // claim SPI bus
    cmdclient.println();
//#ifdef USE_ETHERNET
//    cmdclient.flush();                            // not needed in the end
//    cmdclient.stop();
//#endif
    _releaseSPI();                                  // release SPI bus
    dbgprint("Response send");
  }
}
#endif

//**************************************************************************************************
//                                         C H O M P                                               *
//**************************************************************************************************
// Do some filtering on de inputstring:                                                            *
//  - String comment part (starting with "#").                                                     *
//  - Strip trailing CR.                                                                           *
//  - Strip leading spaces.                                                                        *
//  - Strip trailing spaces.                                                                       *
//**************************************************************************************************
void chomp(String &str)
{
  int inx;                                           // Index in de input string

  if ((inx = str.indexOf("#")) >= 0) {               // Comment line or partial comment?
    str.remove(inx);                                 // Yes, remove
  }
  str.trim();                                        // Remove spaces and CR
}

//**************************************************************************************************
//                                     A N A L Y Z E C M D                                         *
//**************************************************************************************************
// Handling of the various commands from remote webclient or Serial                                *
// Version for handling string with: <parameter>=<value>                                           *
//**************************************************************************************************
const char* analyzeCmd(const char* str)
{
  char*       value;                            // Points to value after equalsign in command
  const char* res;                              // Result of analyzeCmd

  value = strstr(str, "=");                     // See if command contains a "="
  if (value) {
    *value = '\0';                              // Separate command from value
    res = analyzeCmd(str, value + 1);           // Analyze command and handle it
    *value = '=';                               // Restore equal sign
  }
  else {
    res = analyzeCmd(str, "0");                 // No value, assume zero
  }
  return res;
}

//**************************************************************************************************
//                                     A N A L Y Z E C M D                                         *
//**************************************************************************************************
// Handling of the various commands from remote webclient or serial                                *
// par holds the parametername and val holds the value.                                            *
// "wifi_00" and "preset_00" may appear more than once, like wifi_01, wifi_02, etc.                *
// Examples with available parameters:                                                             *
//   preset     = 12                        // Select start preset to connect to                   *
//   preset_00  = <mp3 stream>              // Specify station for a preset 00-99 *)               *
//   toneha     = <0..15>                   // Setting treble gain                                 *
//   tonehf     = <0..15>                   // Setting treble frequency                            *
//   tonela     = <0..15>                   // Setting bass gain                                   *
//   tonelf     = <0..15>                   // Setting treble frequency                            *
//   station    = <mp3 stream>              // Select new station (will not be saved)              *
//   station    = <URL>.mp3                 // Play standalone .mp3 file (not saved)               *
//   station    = <URL>.m3u                 // Select playlist (will not be saved)                 *
//   stop                                   // Stop playing                                        *
//   resume                                 // Resume playing                                      *
//   mute                                   // Mute/unmute the music (toggle)                      *
//   wifi_00    = mySSID/mypassword         // Set WiFi SSID and password *)                       *
//   clk_server = pool.ntp.org              // Time server to be used *)                           *
//   clk_offset = <-11..+14>                // Offset with respect to UTC in hours *)              *
//   clk_dst    = <1..2>                    // Offset during daylight saving time in hours *)      *
//   mp3track   = <nodeIndex>               // Play track from SD card, nodeID 0 = random          *
//   settings                               // Returns setting like presets and tone               *
//   status                                 // Show current URL to play                            *
//   test                                   // For test purposes                                   *
//   debug      = 0 or 1                    // Switch debugging on or off                          *
//   reset                                  // Restart the ESP32                                   *
//  Commands marked with "*)" are sensible during initialization only                              *
//   repeat                                 // repeat cmd                                          *
//   mode                                   // switch between SDCARD / STATION mode                *
//   previous/next                          // previous/next mp3 file or station                   *
//   mediaserver_xxx                        // media server settings                               *
//**************************************************************************************************
const char* analyzeCmd(const char* par, const char* val)
{
  String             argument;                       // Argument as string
  String             value, valout;                  // Value of an argument as a string
  int                ivalue;                         // Value of argument as an integer
  static char        reply[180];                     // Reply to client, will be returned
  //bool               relative;                       // Relative argument (+ or -)
  String             tmpstr;                         // Temporary for value
  uint32_t           av;                             // Available in stream/file

  strcpy(reply, "Command accepted");                 // Default reply
  argument = String(par);                            // Get the argument
  chomp (argument);                                  // Remove comment and useless spaces
  if (argument.length() == 0) {                      // Lege commandline (comment)?
    return reply;                                    // Ignore
  }
  argument.toLowerCase();                            // Force to lower case
  value = String(val);                               // Get the specified value
  chomp (value);                                     // Remove comment and extra spaces
  ivalue = value.toInt();                            // Also as an integer
  ivalue = abs (ivalue);                             // Make positive
  //relative = argument.indexOf("up") == 0;          // + relative setting?
  if (argument.indexOf("down") == 0) {               // - relative setting?
    //relative = true;                                 // It's relative
    ivalue = - ivalue;                               // But with negative value
  }
  if (value.startsWith("http://")) {                 // Does (possible) URL contain "http://"?
    value.remove (0, 7);                             // Yes, remove it
  }
  if (value.length()) {
    tmpstr = value;                                  // Make local copy of value
    if (argument.indexOf("passw") >= 0) {            // Password in value?
      tmpstr = String("*******");                    // Yes, hide it
    }
    dbgprint("Command: %s with parameter %s",
               argument.c_str(), tmpstr.c_str());
  }
  else {
    dbgprint("Command: %s (without parameter)",
               argument.c_str());
  }
  if (argument.indexOf("volume") == 0) {             // absolute Volume setting?
    ini_block.reqvol = ivalue;
    if (ini_block.reqvol < 60) {
      ini_block.reqvol = 60;                         // Limit to min value 60
    }
    else if (ini_block.reqvol > 92) {
      ini_block.reqvol = 92;                         // Limit to value 92
    }
    muteFlag = 0;                                    // Stop possibly muting
    sprintf(reply, "Volume is now %d",               // Reply new volume
              ini_block.reqvol);
  }
  else if (argument.indexOf("volume") > 0) {         // relative Volume setting?
    ini_block.reqvol += ivalue;
    if (ini_block.reqvol < 60) {
      ini_block.reqvol = 60;                         // Limit to min value 60
    }
    else if (ini_block.reqvol > 92) {
      ini_block.reqvol = 92;                         // Limit to max value 92
    }
    muteFlag = 0;                                    // Stop possibly muting
    sprintf(reply, "Volume is now %d",               // Reply new volume
            ini_block.reqvol);
  }
  else if (argument == "mute") {                     // Mute/unmute request
    muteFlag = (!muteFlag) ? -1 : 0;
    sprintf(reply, "Output is now %s",               // Reply mute status
            muteFlag ? "muted" : "unmuted");
  }
  else if (argument == "repeat") {                   // repeate request
    if (currentSource == SDCARD && currentIndex > 0 &&
         playMode == SDCARD && SD_okay) {
      if (mp3fileRepeatFlag == NOREPEAT) {
        mp3fileRepeatFlag = SONG;                    // repeat same file
        sprintf(reply, "Repeat Mode = SONG");
      }
      else if (mp3fileRepeatFlag == SONG) {
        mp3fileRepeatFlag = DIRECTORY;               // repeat same directory
        sprintf(reply, "Repeat Mode = DIRECTORY");
      }
      else if (mp3fileRepeatFlag == DIRECTORY) {
        mp3fileRepeatFlag = RANDOM;                  // random play
        sprintf(reply, "Repeat Mode = RANDOM");
      }
      else {
        mp3fileRepeatFlag = NOREPEAT;                // clear repeat flag
        sprintf(reply, "Repeat Mode = NOREPEAT");
      }
    }
    else if (currentSource == MEDIASERVER && currentIndex >= 0) {
      if (mp3fileRepeatFlag == NOREPEAT) {
        mp3fileRepeatFlag = SONG;                    // repeat same file
        sprintf(reply, "Repeat Mode = SONG");
      }
      else if (mp3fileRepeatFlag == SONG) {
        mp3fileRepeatFlag = DIRECTORY;               // repeat same directory
        sprintf(reply, "Repeat Mode = DIRECTORY");
      }
      else if (mp3fileRepeatFlag == DIRECTORY) {
        mp3fileRepeatFlag = NOREPEAT;               // repeat same directory
        sprintf(reply, "Repeat Mode = NOREPEAT");
      }
    }
    else {
      sprintf(reply, "Command \'Repeat\' not allowed in this state.");
    }
  }
  else if (argument.indexOf("ir_") >= 0) {           // Ir setting?
    // No action required
  }
  else if (argument.indexOf("preset_") >= 0) {       // Enumerated preset?
    // No action required
  }
  else if (argument.indexOf("preset") == 0) {        // Preset station?
    mp3fileRepeatFlag = NOREPEAT;  
    playMode = STATION;
    ini_block.newpreset = ivalue;                    // Otherwise set station
    playlist_num = 0;                                // Absolute, reset playlist
    sprintf(reply, "Preset is now %d",               // Reply new preset
            ini_block.newpreset);
  }
  else if (argument.indexOf("pause") >= 0) {
    // TEST
    //dbgprint("dataMode=%d, playMode=%d, totalCount=%d, currentSource=%d, currentPreset=%d, encoderMode=%d",
    //            dataMode, playMode, totalCount, currentSource, currentPreset, encoderMode);
    if (dataMode == DATA && currentSource == SDCARD &&
         playMode == SDCARD && SD_okay && currentIndex > 0) {
      mp3filePause = !mp3filePause;
      sprintf(reply, "Playing mp3 file %s",              // Reply pause status
                mp3filePause ? "has paused." : "continues.");
      if (mp3filePause) {
        xQueueReset (dataQueue);
      }
      else {
        //muteFlag = 6;                                     // suppresses chirps
      }
    }
    else {
      sprintf(reply, "Command \'Pause\' not allowed in this state.");
    }
  }
  else if (argument.indexOf("previous") >= 0 ||
           argument.indexOf("downpreset") >= 0) {
    if (currentSource == SDCARD && playMode == SDCARD) {
      if (SD_okay && currentIndex > 0) {
        int fileIndex;                                  // Previous file index of track on SD
        if (mp3fileRepeatFlag == SONG ||
             ((mp3fileLength - mp3fileBytesLeft) > (mp3fileLength / 30)))
          fileIndex = currentIndex;                     // Select the same file again
        else if (mp3fileRepeatFlag == NOREPEAT)
          fileIndex = nextSDfileIndex(currentIndex, -1); // Select the previous file on SD
        else if (mp3fileRepeatFlag == DIRECTORY)
          fileIndex = nextSDfileIndexInSameDir(currentIndex, -1); // select previous file in same directory
        else
          fileIndex = 0;                                // random mode
        host = getSDfilename(fileIndex);
        if (host.startsWith("error")) {
          dbgprint("SD problem: can't find file with index %d", fileIndex);
        }
        else {
          dbgprint("STOP (command: previous file on SD)");
          dataMode = STOPREQD;                          // Request STOP
          hostreq = true;                               // Request this host
          sprintf(reply, "Next playing %s", host.c_str());
          utf8ascii(reply);
          muteFlag = 10;
        }
      }
    }
    else if (currentSource == STATION && playMode == STATION) {
      xQueueReset (dataQueue);
      muteFlag = 30;
      ini_block.newpreset -= 1;                         // Yes, adjust currentPreset
      if (ini_block.newpreset < 0)
        ini_block.newpreset = highestPreset;
      sprintf(reply, "Preset is now %d",                // Reply new preset
                     ini_block.newpreset);
    }
#ifdef ENABLE_SOAP    
    else if (currentSource == MEDIASERVER && playMode == MEDIASERVER) {
      const char* p;
      int16_t newIndex;

      if (mp3fileRepeatFlag == SONG ||
            ((mp3fileLength - mp3fileBytesLeft) > (mp3fileLength / 30))) {
        newIndex = currentIndex;                        // Select the same file again
      }  
      else {
        newIndex = nextSoapFileIndex(currentIndex, -1); // Select the previous file on soap list
      }
      if (newIndex != -1) {
        p = dbgprint("Next playing \"%s\"", soapList[newIndex].name.c_str());
        host = "soap/" + soapList[newIndex].uri;
        hostObject = soapList[newIndex];
        currentIndex = newIndex;
        dbgprint("STOP (command: previous file in soap list)");
        dataMode = STOPREQD;                            // Request STOP
        hostreq = true;                                 // Request this host
        muteFlag = 10;
      }
      else {
        p = dbgprint("Soap list problem: can't find previous entry");
      }
      strcpy(reply, p);
      utf8ascii(reply);  
    }
#endif
  }
  else if (argument.indexOf("next") >= 0 ||
           argument.indexOf("uppreset") >= 0) {
    if (currentSource == SDCARD && playMode == SDCARD) {
      if (SD_okay && currentIndex > 0) {
        int fileIndex;                                               // Next file index of track on SD
        if (!mp3fileRepeatFlag)
          fileIndex = nextSDfileIndex (currentIndex, +1);            // Select the next file on SD
        else if (mp3fileRepeatFlag == SONG)
          fileIndex = currentIndex;                                  // Select the same file
        else if (mp3fileRepeatFlag == DIRECTORY)
          fileIndex = nextSDfileIndexInSameDir (currentIndex, +1);   // select next file in same directory
        else
          fileIndex = 0;                                             // random mode
        host = getSDfilename (fileIndex);
        if (host.startsWith("error")) {
          dbgprint("SD problem: can't find file with index %d", fileIndex);
        }
        else {
          dbgprint("STOP (command: next file on SD)");
          dataMode = STOPREQD;                          // Request STOP
          hostreq = true;                               // Request this host
          sprintf(reply, "Next playing: %s", host.c_str());
          utf8ascii(reply);
          muteFlag = 10;
        }
      }
    }
    else if (currentSource == STATION && playMode == STATION) {
      xQueueReset (dataQueue);
      muteFlag = 30;
      ini_block.newpreset += 1;                         // Yes, adjust currentPreset
      if (ini_block.newpreset > highestPreset)
        ini_block.newpreset = 0;
      sprintf(reply, "Preset is now %d",                // Reply new preset
                ini_block.newpreset);
    }
#ifdef ENABLE_SOAP    
    else if (currentSource == MEDIASERVER && playMode == MEDIASERVER) {
      const char* p;
      int16_t newIndex;

      if (mp3fileRepeatFlag == SONG) {
        newIndex = currentIndex;                        // Select the same file again
      }  
      else {
        newIndex = nextSoapFileIndex(currentIndex, +1); // Select the next file on soap list
      }
      if (newIndex != -1) {
        p = dbgprint("Next playing: \"%s\"", soapList[newIndex].name.c_str());
        host = "soap/" + soapList[newIndex].uri;
        hostObject = soapList[newIndex];
        currentIndex = newIndex;
        dbgprint("STOP (command: next file in soap list)");
        dataMode = STOPREQD;                            // Request STOP
        hostreq = true;                                 // Request this host
        muteFlag = 10;
      }
      else {
        p = dbgprint("Soap list problem: Can't find next entry");
      }
      strcpy(reply, p);
      utf8ascii(reply);  
    }
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
