yellobyte/ESP32-Webradio-PlusDLNA/Software/include/SansSerif_plain_14.h

// Created by http://oleddisplay.squix.ch/ Consider a donation
// In case of problems make sure that you are using the font file with the correct version!
const uint8_t SansSerif_plain_14Bitmaps[] PROGMEM = {

	// Bitmap Data:
	0x00, // ' '
	0xFC,0xC0, // '!'
	0xB6,0xD0, // '"'
	0x09,0x02,0x40,0x91,0xFF,0x12,0x04,0x8F,0xF8,0x98,0x24,0x09,0x00, // '#'
	0x10,0x21,0xF4,0x99,0x1A,0x1F,0x0B,0x13,0x25,0xF0,0x81,0x00, // '$'
	0x70,0x88,0x88,0x89,0x08,0xB0,0x8A,0xE7,0x51,0x0D,0x10,0x91,0x11,0x11,0x0E, // '%'
	0x38,0x11,0x04,0x00,0x80,0x50,0x22,0x18,0x46,0x0A,0x43,0x0F,0x30, // '&'
	0xF0, // '''
	0x69,0x49,0x24,0x89,0x10, // '('
	0x89,0x12,0x49,0x29,0x40, // ')'
	0x11,0x25,0xF1,0xCD,0x62,0x00, // '*'
	0x08,0x04,0x02,0x01,0x0F,0xF8,0x40,0x20,0x10,0x08,0x00, // '+'
	0x58, // ','
	0xF0, // '-'
	0xC0, // '.'
	0x08,0xC4,0x23,0x10,0x8C,0x42,0x31,0x00, // '/'
	0x38,0x8A,0x0C,0x18,0x30,0x60,0xC1,0x44,0x70, // '0'
	0x65,0x08,0x42,0x10,0x84,0x27,0xC0, // '1'
	0x7A,0x30,0x41,0x0C,0x21,0x08,0x43,0xF0, // '2'
	0x7D,0x0C,0x08,0x13,0xC0,0xC0,0x81,0x86,0xF0, // '3'
	0x0C,0x28,0x91,0x24,0x50,0xBF,0x82,0x04,0x08, // '4'
	0xFD,0x02,0x07,0xC8,0x40,0x40,0x81,0x84,0xF0, // '5'
	0x3C,0xC7,0x04,0x0B,0xD8,0xE0,0xC1,0x46,0x78, // '6'
	0xFE,0x08,0x10,0x40,0x82,0x04,0x10,0x20,0x80, // '7'
	0x7D,0x8E,0x0E,0x33,0x98,0xE0,0xC1,0xC6,0xF8, // '8'
	0x79,0x8A,0x0C,0x1C,0x6F,0x40,0x83,0x8C,0xF0, // '9'
	0xC6, // ':'
	0x50,0x16, // ';'
	0x00,0x83,0x8E,0x1C,0x0E,0x01,0xC0,0x1C,0x01, // '<'
	0xFF,0x80,0x00,0x1F,0xF0, // '='
	0x80,0x38,0x03,0x80,0x70,0x38,0x71,0xC1,0x00, // '>'
	0x74,0x42,0x33,0x10,0x80,0x21,0x00, // '?'
	0x0F,0x83,0x04,0x40,0x24,0xE9,0x99,0x99,0x09,0x90,0x99,0x9A,0x4E,0xC4,0x00,0x30,0x40,0xF8, // '@'
	0x08,0x0A,0x05,0x04,0x42,0x21,0x11,0xFC,0x82,0x41,0x40,0x40, // 'A'
	0xFE,0x83,0x81,0x83,0xFE,0x83,0x81,0x81,0x83,0xFE, // 'B'
	0x3E,0x61,0xC0,0x80,0x80,0x80,0x80,0xC0,0x61,0x3E, // 'C'
	0xFC,0x41,0xA0,0x70,0x18,0x0C,0x06,0x03,0x03,0x83,0x7E,0x00, // 'D'
	0xFF,0x02,0x04,0x0F,0xF0,0x20,0x40,0x81,0xFC, // 'E'
	0xFE,0x08,0x20,0xFE,0x08,0x20,0x82,0x00, // 'F'
	0x1F,0x30,0x50,0x10,0x08,0x04,0x1E,0x02,0x81,0x60,0x8F,0x80, // 'G'
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
};
const GFXglyph SansSerif_plain_14Glyphs[] PROGMEM = {
// bitmapOffset, width, height, xAdvance, xOffset, yOffset
	  {     0,   1,   1,   5,    0,    0 }, // ' '
	  {     1,   1,  10,   6,    2,  -10 }, // '!'
	  {     3,   3,   4,   6,    1,  -10 }, // '"'
	  {     5,  10,  10,  13,    1,  -10 }, // '#'
	  {    18,   7,  13,  10,    1,  -11 }, // '$'
	  {    30,  12,  10,  14,    0,  -10 }, // '%'
	  {    45,  10,  10,  13,    1,  -10 }, // '&'
	  {    58,   1,   4,   4,    1,  -10 }, // '''
	  {    59,   3,  12,   6,    1,  -11 }, // '('
	  {    64,   3,  12,   6,    1,  -11 }, // ')'
	  {    69,   7,   6,   8,    0,  -10 }, // '*'
	  {    75,   9,   9,  13,    1,   -9 }, // '+'
	  {    86,   2,   3,   5,    1,   -2 }, // ','
	  {    87,   4,   1,   6,    1,   -4 }, // '-'
	  {    88,   1,   2,   5,    2,   -2 }, // '.'
	  {    89,   5,  12,   6,    0,  -10 }, // '/'
	  {    97,   7,  10,  10,    1,  -10 }, // '0'
	  {   106,   5,  10,  10,    2,  -10 }, // '1'
	  {   113,   6,  10,  10,    1,  -10 }, // '2'
	  {   121,   7,  10,  10,    1,  -10 }, // '3'
	  {   130,   7,  10,  10,    1,  -10 }, // '4'
	  {   139,   7,  10,  10,    1,  -10 }, // '5'
	  {   148,   7,  10,  10,    1,  -10 }, // '6'
	  {   157,   7,  10,  10,    1,  -10 }, // '7'
	  {   166,   7,  10,  10,    1,  -10 }, // '8'
	  {   175,   7,  10,  10,    1,  -10 }, // '9'
	  {   184,   1,   7,   6,    2,   -7 }, // ':'
	  {   185,   2,   8,   6,    1,   -7 }, // ';'
	  {   187,   9,   8,  13,    1,   -8 }, // '<'
	  {   196,   9,   4,  13,    1,   -7 }, // '='
	  {   201,   9,   8,  13,    1,   -8 }, // '>'
	  {   210,   5,  10,   8,    1,  -10 }, // '?'
	  {   217,  12,  12,  15,    1,  -10 }, // '@'
	  {   235,   9,  10,  10,    0,  -10 }, // 'A'
	  {   247,   8,  10,  11,    1,  -10 }, // 'B'
	  {   257,   8,  10,  11,    1,  -10 }, // 'C'
	  {   267,   9,  10,  12,    1,  -10 }, // 'D'
	  {   279,   7,  10,  10,    1,  -10 }, // 'E'
	  {   288,   6,  10,   9,    1,  -10 }, // 'F'
	  {   296,   9,  10,  12,    1,  -10 }, // 'G'
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
};
const GFXfont SansSerif_plain_14 PROGMEM = {
(uint8_t  *)SansSerif_plain_14Bitmaps,(GFXglyph *)SansSerif_plain_14Glyphs,0x20, 0x7E, 17};
