yellobyte/ESP32-Webradio-PlusDLNA/Software/add_tasks.py

Import("env")
env.AddCustomTarget(
    name="envdump",
    dependencies=None,
    actions=[
        "pio run -t envdump",
    ],
    title="Show Build Options [envdump]",
    description="Show Build Options "
)
env.AddCustomTarget(
    name="prune",
    dependencies=None,
    actions=[
        "pio system prune -f",
    ],
    title="Prune System",
    description="Prune System"
)
